Tenejakin/LM1/output/pdf/lm1-apriltag-36h11-id0-100mm-v1.0.0.pdf

# LM1 Camera Calibration Tag

AprilTag 36h11 - ID 0 - black outside edge is exactly 100 mm

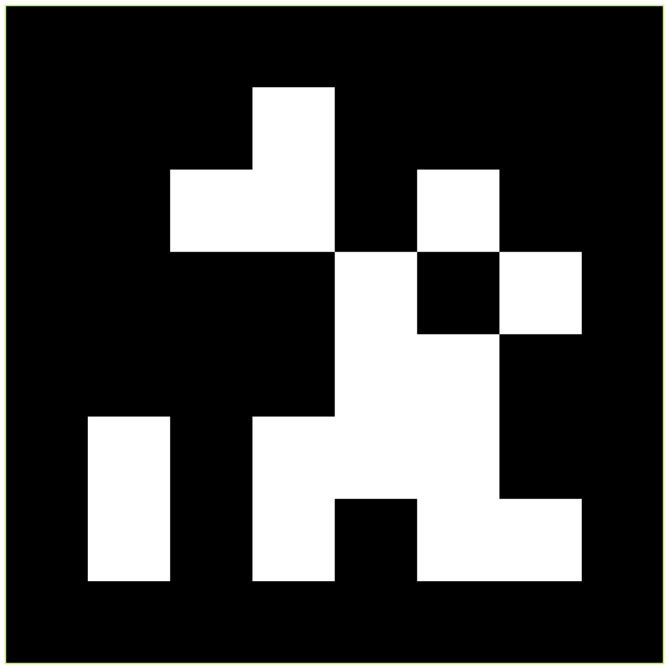
[picture p2: figure]

Use it to calibrate, then remove it before the hit.

1. Print at 100% / Actual size. Do not use Fit to page.
2. Measure the green outline: it must be 100 mm on every side.
3. Lay it flat beside the ball, capture calibration, then remove it without moving camera or mat.
4. Recalibrate whenever the camera, hitting mat, or ball location moves.
0 | 10 | 20 | 30 | 40 | 50 | 60 | 70 | 80 | 90 | 100

100 mm print check

LM1 AprilTag target v1.0.0 - keep flat, clean, and evenly lit
