Tenejakin/LM1/hardware/enclosure/stl/v0.6.0-stereo/preview.png

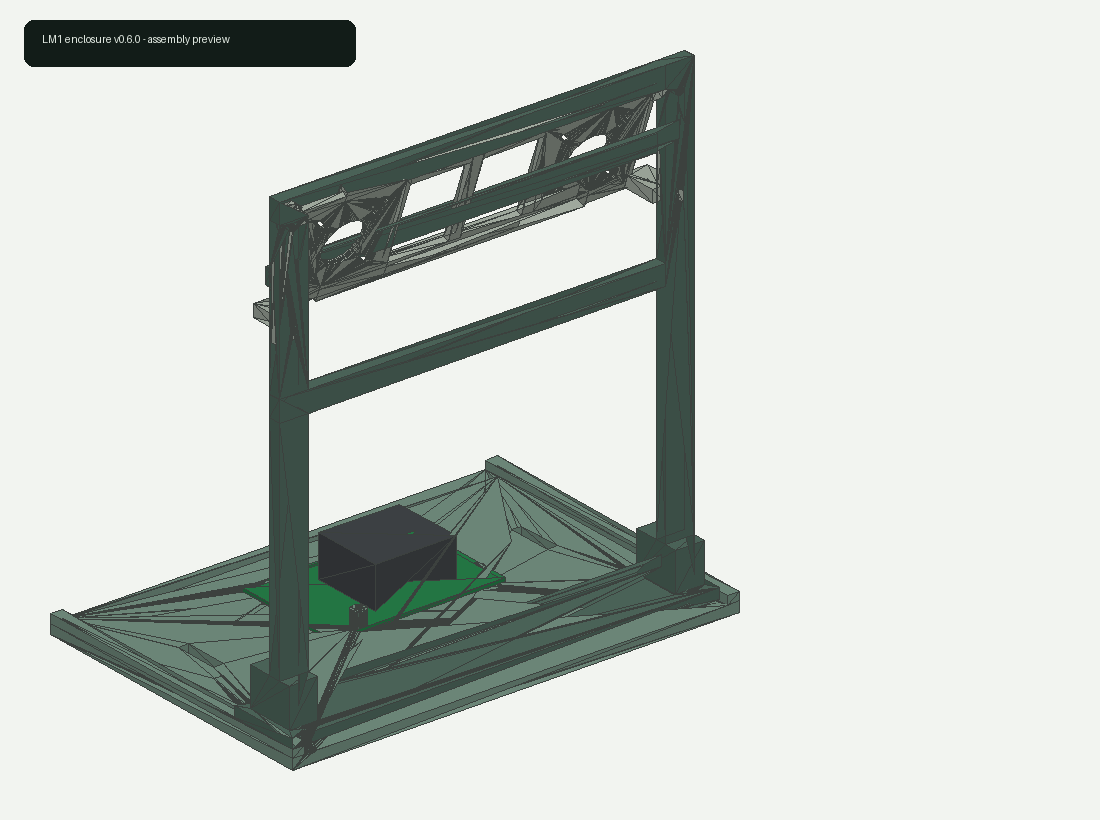
hardware/enclosure/stl/v0.6.0-stereo/preview.png
