Tenejakin/LM1/hardware/enclosure/stl/v0.7.2-vertical-development/preview.png

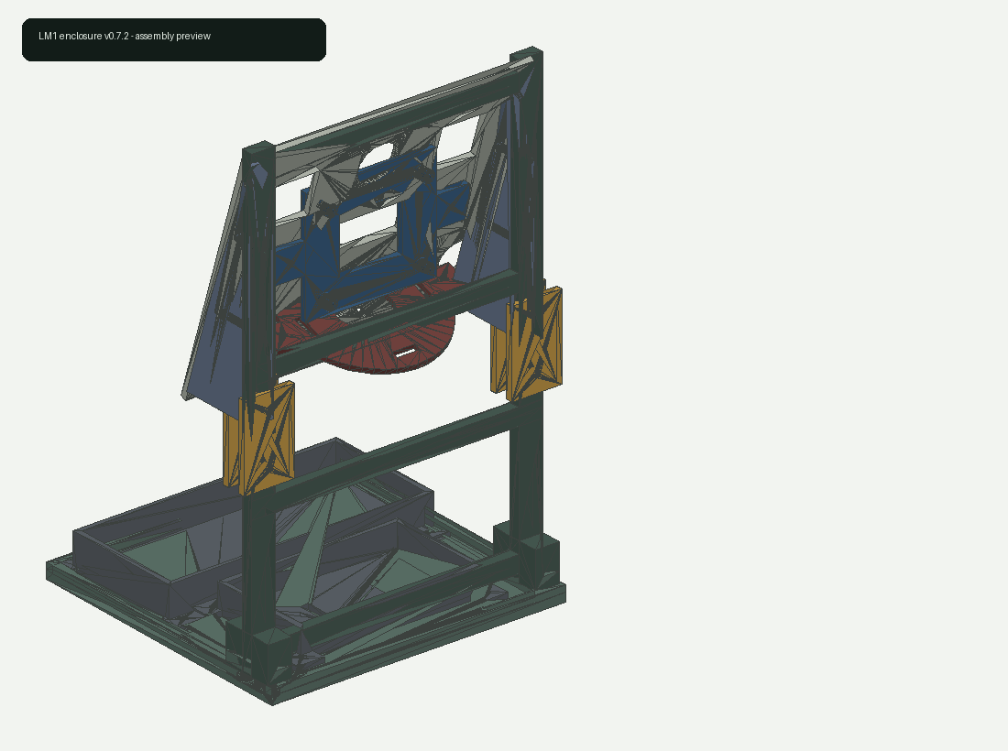
hardware/enclosure/stl/v0.7.2-vertical-development/preview.png
