Tenejakin/LM1/hardware/ir-crossbar-v1.0.1/preview.png

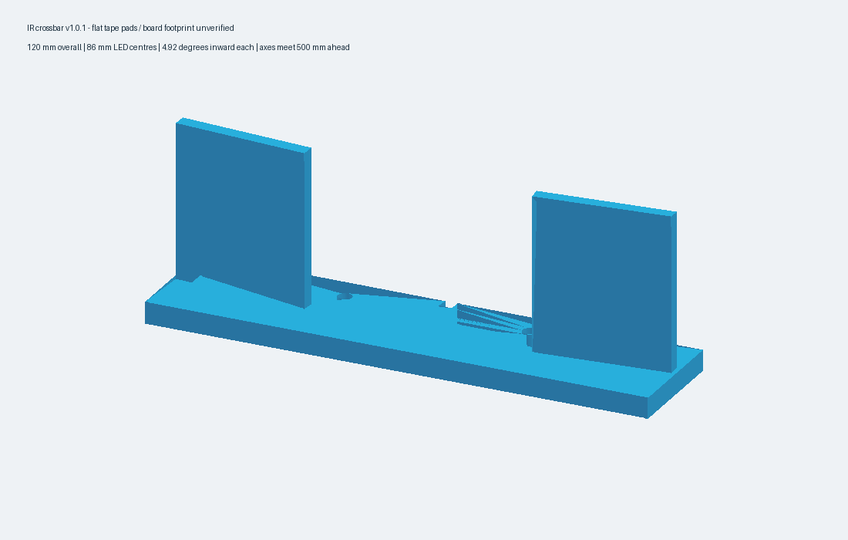
hardware/ir-crossbar-v1.0.1/preview.png
