Tenejakin/LM1/output/ir-denoise-v1.0.0/bilateral-display-4x.png

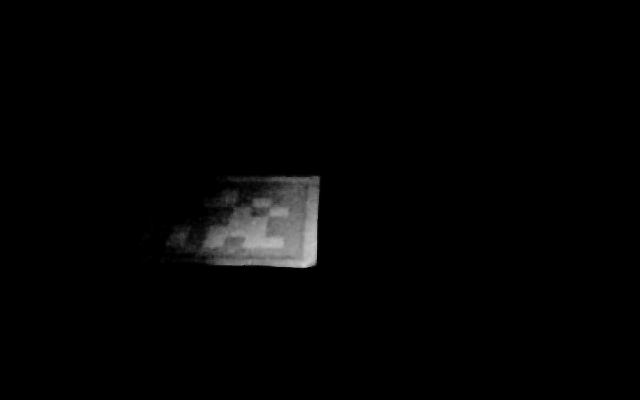
output/ir-denoise-v1.0.0/bilateral-display-4x.png
