Tenejakin/LM1/output/tag-recovery-v1.0.0/clahe.png

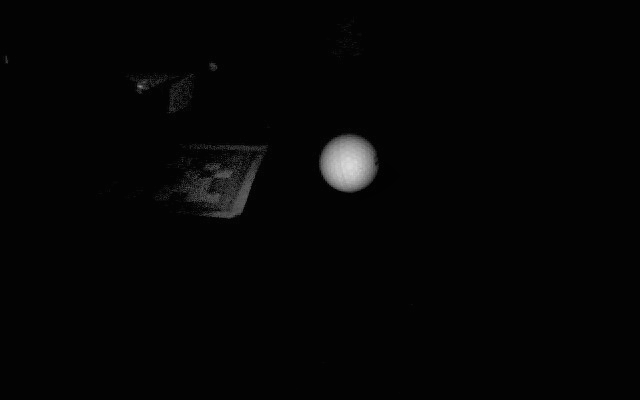
output/tag-recovery-v1.0.0/clahe.png
