Tenejakin/LM1/tmp/ai-review-latest/armed-ball-reference.png

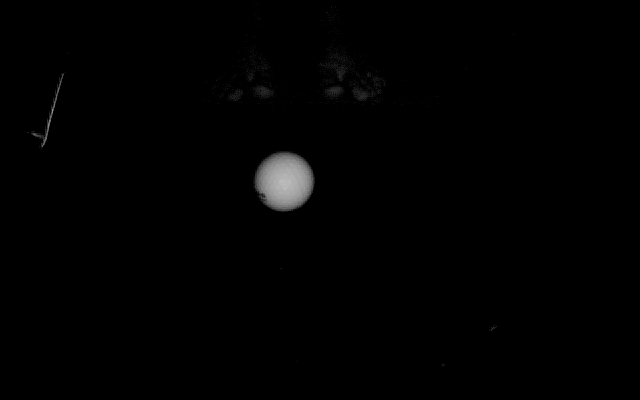
tmp/ai-review-latest/armed-ball-reference.png
