Tenejakin/LM1/tmp/ai-review-latest/frame-0175.jpg

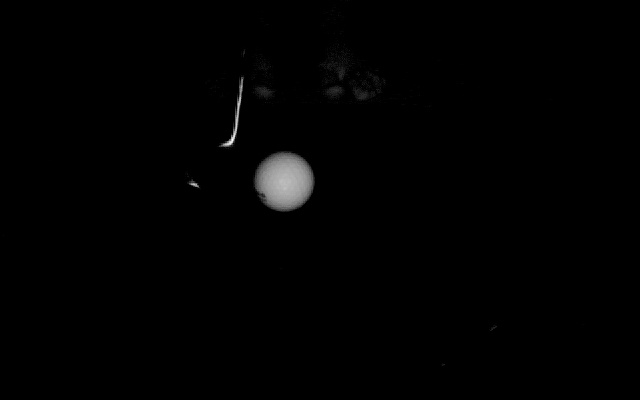
tmp/ai-review-latest/frame-0175.jpg
