Tenejakin/LM1/tmp/ai-review-latest/frame-0179.jpg

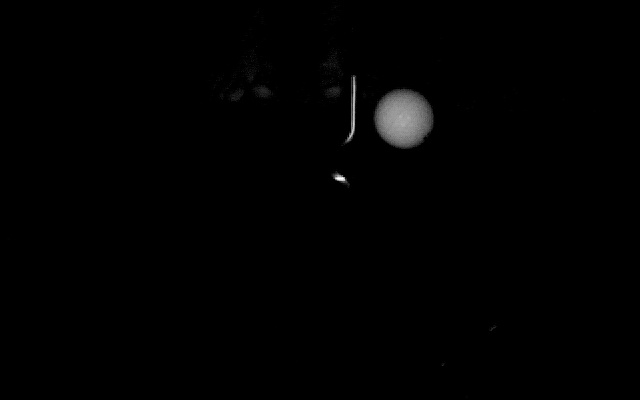
tmp/ai-review-latest/frame-0179.jpg
