Tenejakin/LM1/tmp/ai-review-latest/frame-0180.jpg

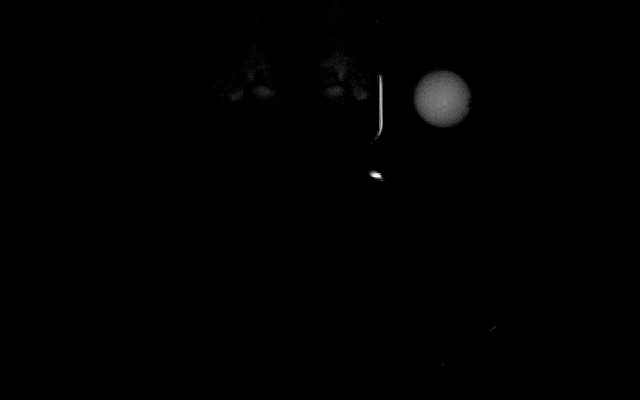
tmp/ai-review-latest/frame-0180.jpg
