Tenejakin/LM1/tmp/ai-review-latest/frame-0182.jpg

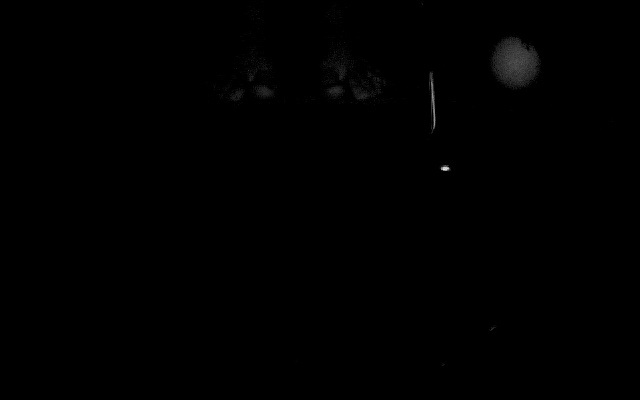
tmp/ai-review-latest/frame-0182.jpg
