Tenejakin/LM1/tmp/ai-review-marked-ball/frame-0185.jpg

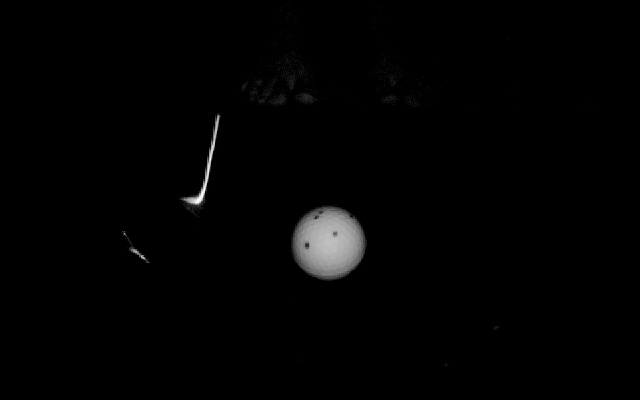
tmp/ai-review-marked-ball/frame-0185.jpg
