Tenejakin/LM1/tmp/ai-review-marked-ball/frame-0189.jpg

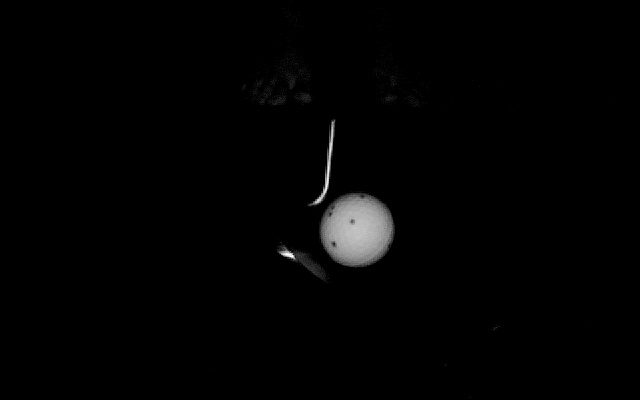
tmp/ai-review-marked-ball/frame-0189.jpg
