Tenejakin/LM1/tmp/ai-review-marked-ball/frame-0190.jpg

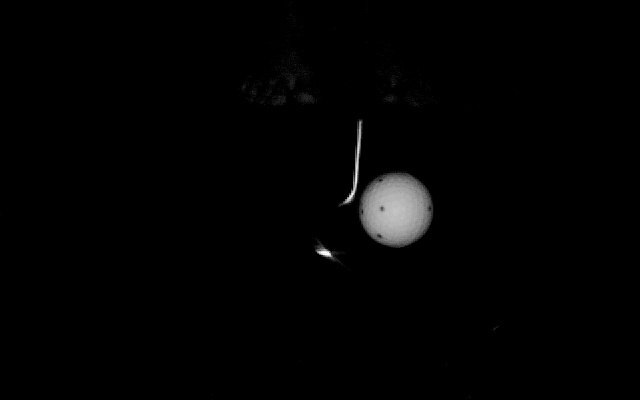
tmp/ai-review-marked-ball/frame-0190.jpg
