Tenejakin/LM1/tmp/ai-review-marked-ball/frame-0191.jpg

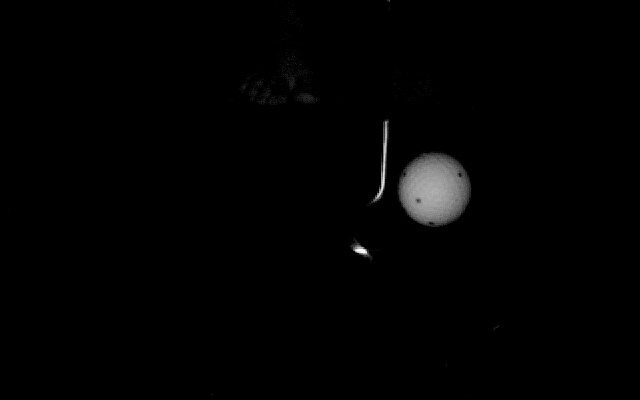
tmp/ai-review-marked-ball/frame-0191.jpg
