Tenejakin/LM1/tmp/ai-review-marked-ball/frame-0194.jpg

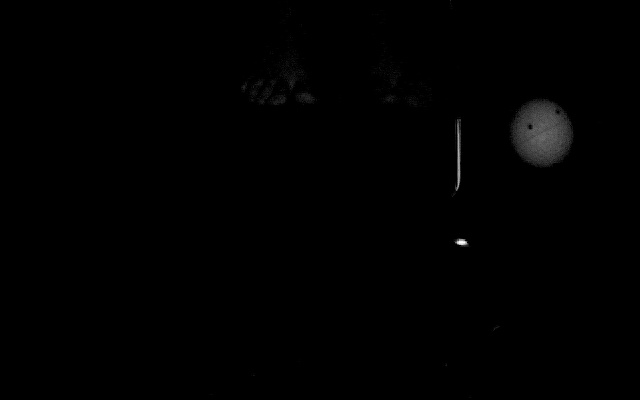
tmp/ai-review-marked-ball/frame-0194.jpg
