Tenejakin/LM1/tmp/ai-review-marked-ball/frame-0198.jpg

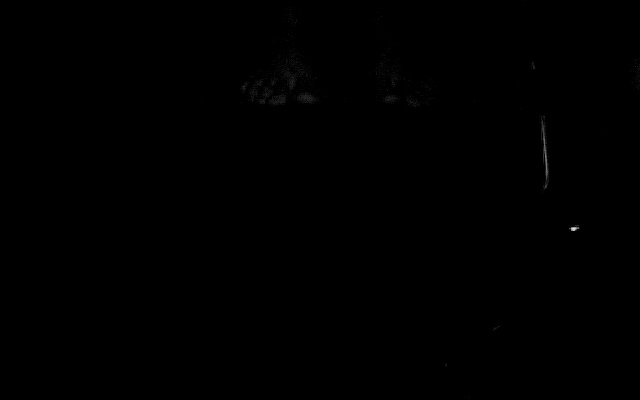
tmp/ai-review-marked-ball/frame-0198.jpg
