Tenejakin/LM1/tmp/apriltag/live-ball-after-reset.jpg

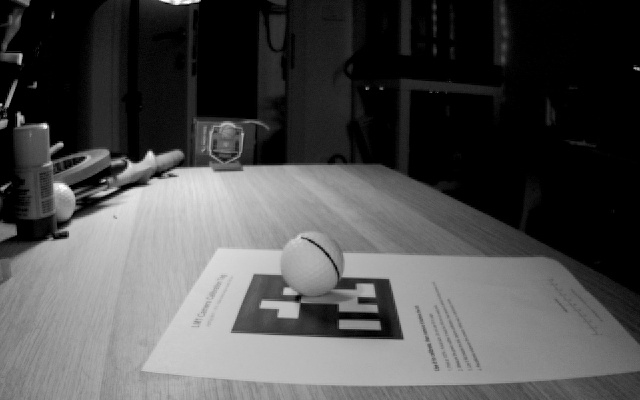
tmp/apriltag/live-ball-after-reset.jpg
