Tenejakin/LM1/tmp/apriltag/live-ball-diagnostic.jpg

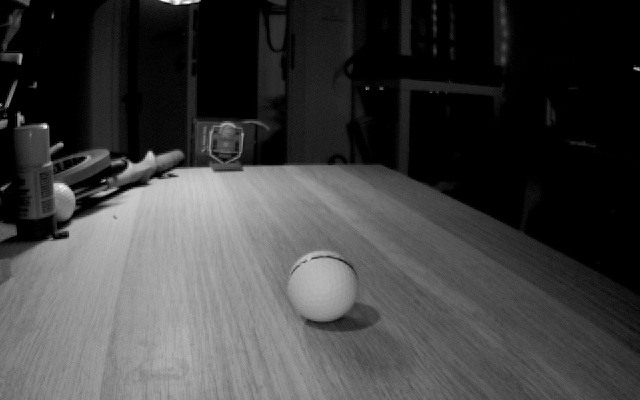
tmp/apriltag/live-ball-diagnostic.jpg
