Tenejakin/LM1/tmp/apriltag/live-ball-moved.jpg

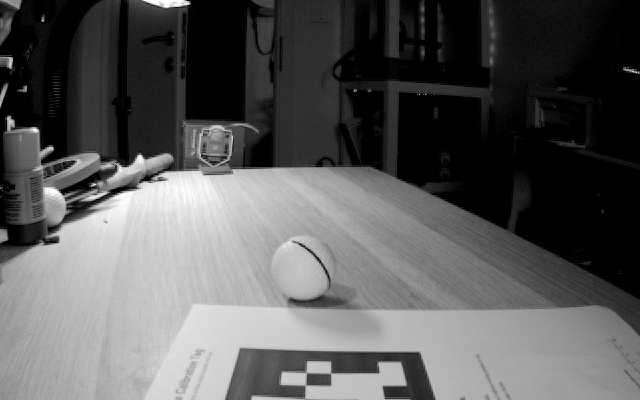
tmp/apriltag/live-ball-moved.jpg
