Tenejakin/LM1/tmp/apriltag/pre-0132-restart.jpg

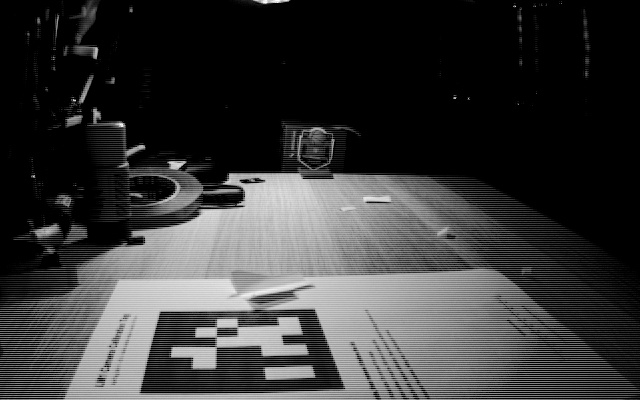
tmp/apriltag/pre-0132-restart.jpg
