Tenejakin/LM1/tmp/apriltag/render/page-1.png

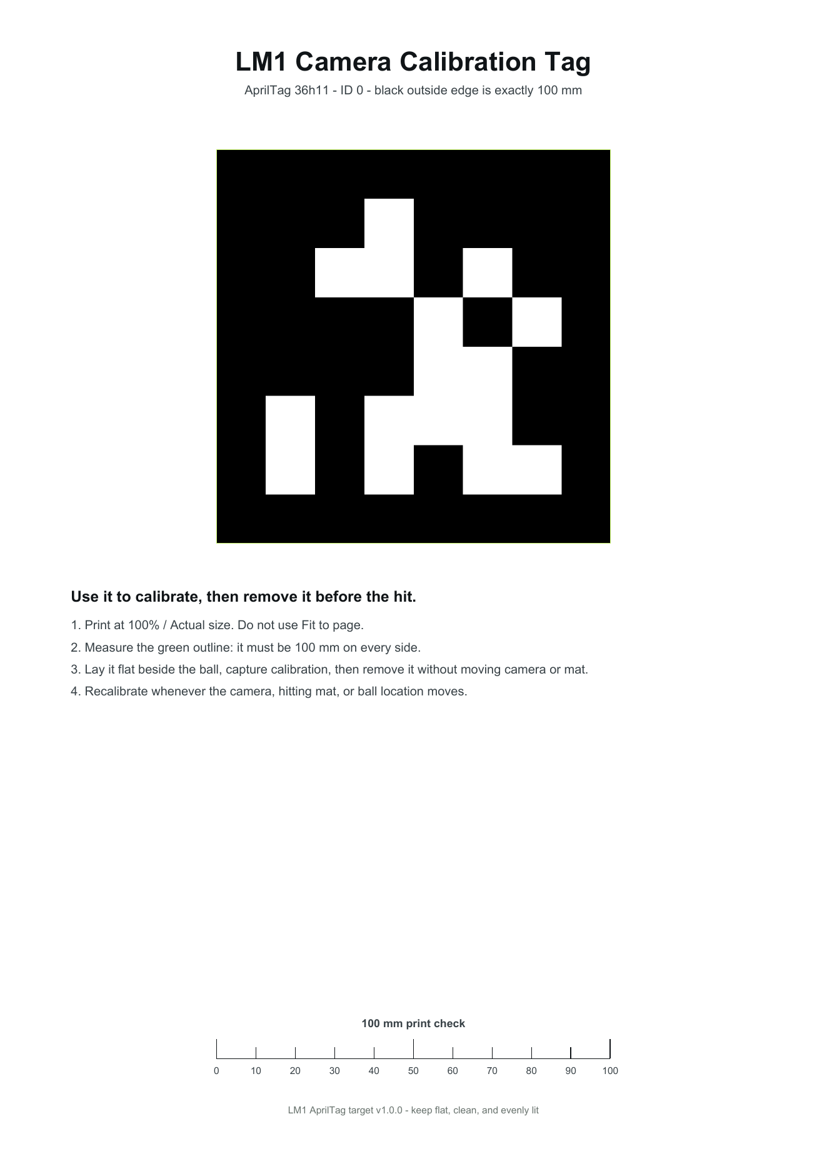
tmp/apriltag/render/page-1.png
