Tenejakin/LM1/tmp/camera-latest-focus-check-gain-current.jpg

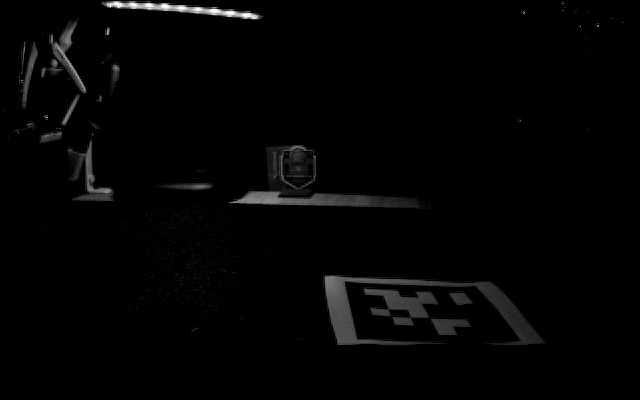
tmp/camera-latest-focus-check-gain-current.jpg
