Tenejakin/LM1/tmp/camera-latest-focus-check.jpg

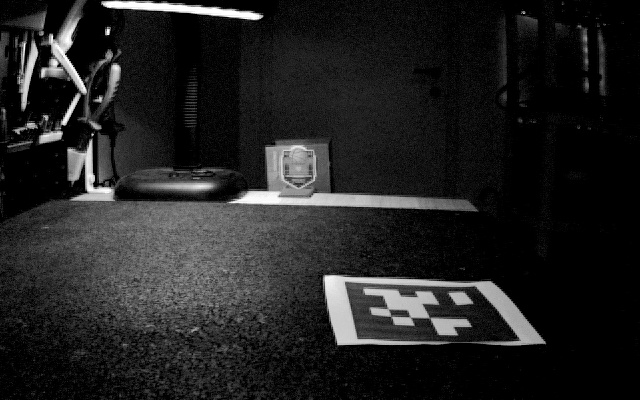
tmp/camera-latest-focus-check.jpg
