Tenejakin/LM1/tmp/camera-snapshot-2026-09-15-1404-v1.0.0.jpg

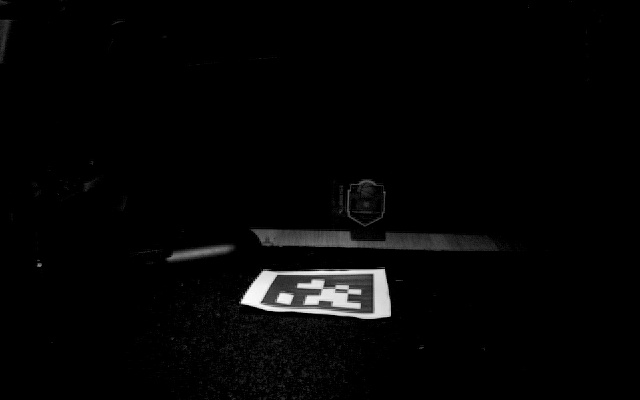
tmp/camera-snapshot-2026-09-15-1404-v1.0.0.jpg
