Tenejakin/LM1/tmp/ir-latest-review/contact-sheet.jpg

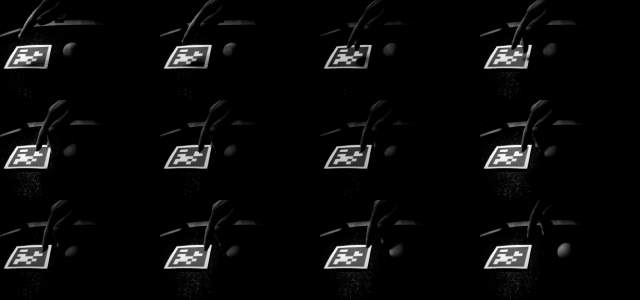
tmp/ir-latest-review/contact-sheet.jpg
