Tenejakin/LM1/tmp/ir-latest-review/ir-current-v1.0.0.jpg

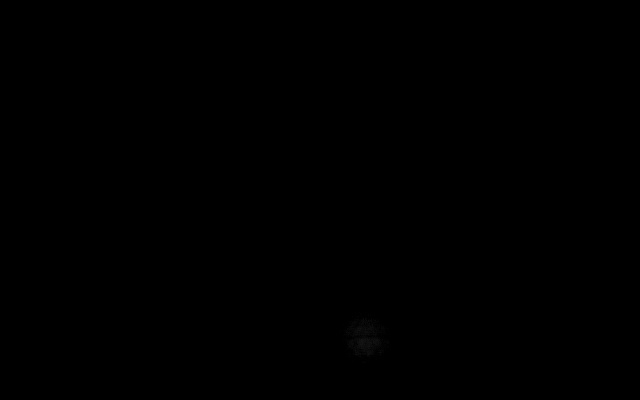
tmp/ir-latest-review/ir-current-v1.0.0.jpg
