Tenejakin/LM1/tmp/ir-latest-review/ir-current-v1.0.1.jpg

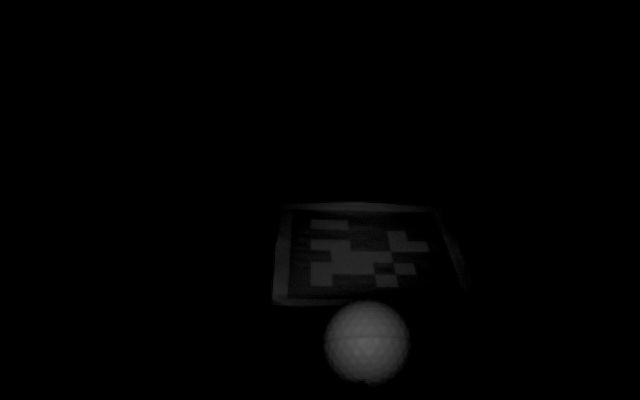
tmp/ir-latest-review/ir-current-v1.0.1.jpg
