Tenejakin/LM1/tmp/last-capture-1789337222749633794/frame-0422.jpg

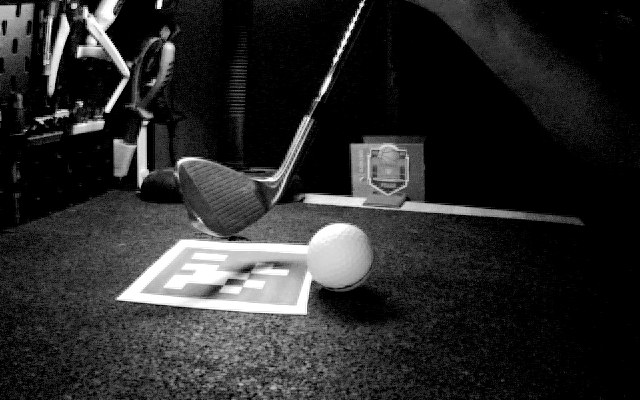
tmp/last-capture-1789337222749633794/frame-0422.jpg
