Tenejakin/LM1/tmp/last-shot-1789389599416398352/contact-sheet.jpg

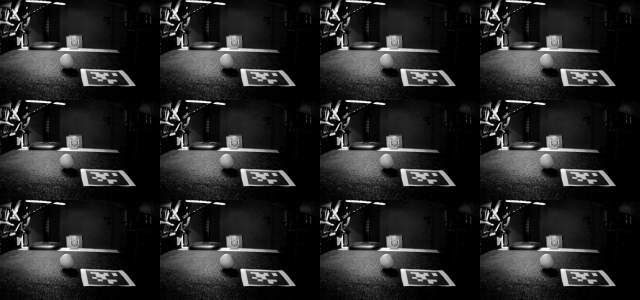
tmp/last-shot-1789389599416398352/contact-sheet.jpg
