Tenejakin/LM1/tmp/last-shot/contact-sheet.jpg

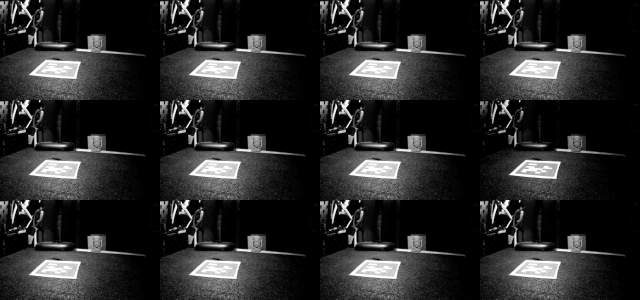
tmp/last-shot/contact-sheet.jpg
