Tenejakin/LM1/tmp/last-shot/frame-0410.jpg

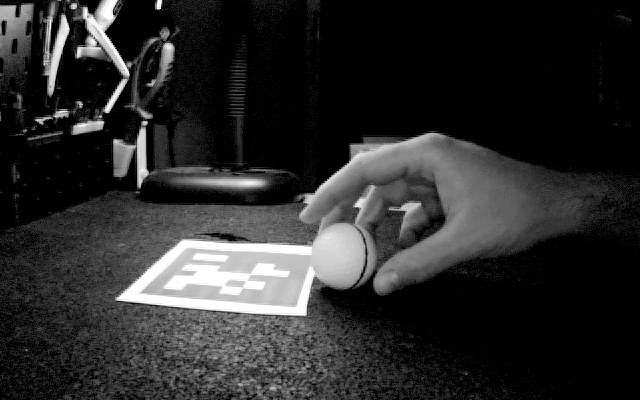
tmp/last-shot/frame-0410.jpg
