Tenejakin/LM1/tmp/last-shot/frame-0435.jpg

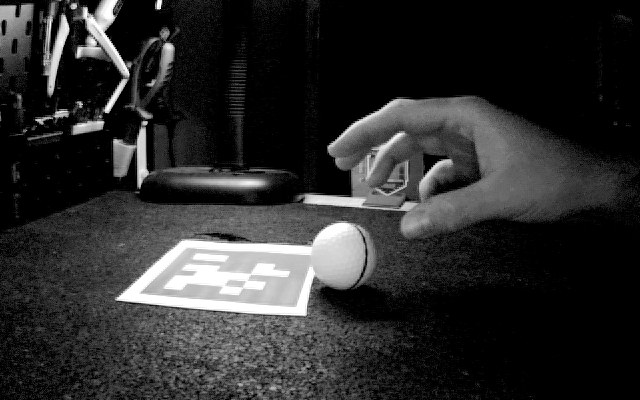
tmp/last-shot/frame-0435.jpg
