Tenejakin/LM1/tmp/last-shot/frame-0450.jpg

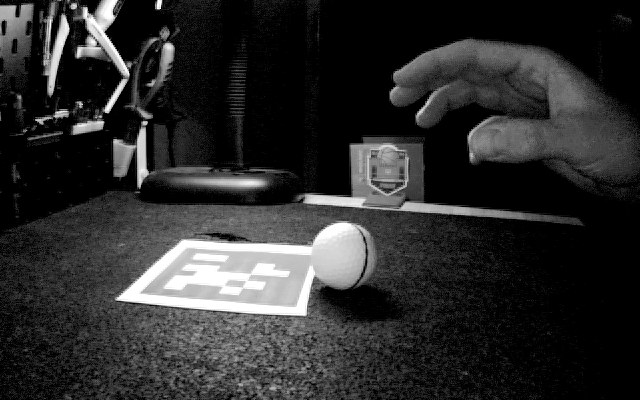
tmp/last-shot/frame-0450.jpg
