Tenejakin/LM1/tmp/last-shot/frame-0454.jpg

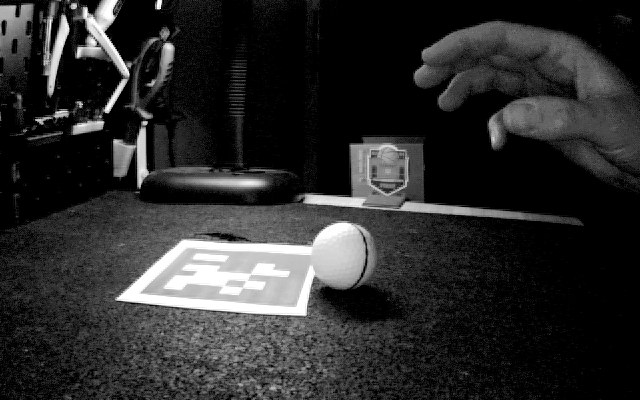
tmp/last-shot/frame-0454.jpg
