Tenejakin/LM1/tmp/last-shot/frame-0500.jpg

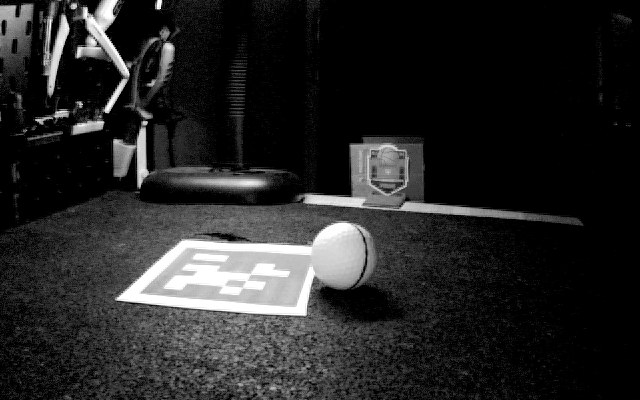
tmp/last-shot/frame-0500.jpg
