Tenejakin/LM1/tmp/rolling-review/capture-1788818826306235541/frame-0128.jpg

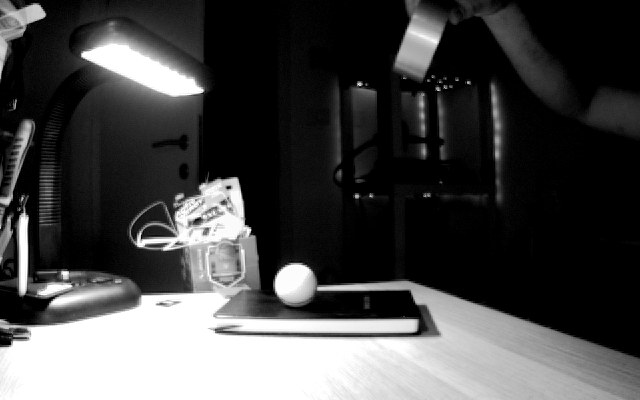
tmp/rolling-review/capture-1788818826306235541/frame-0128.jpg
