Tenejakin/LM1/tmp/shot2/frame-0300.jpg

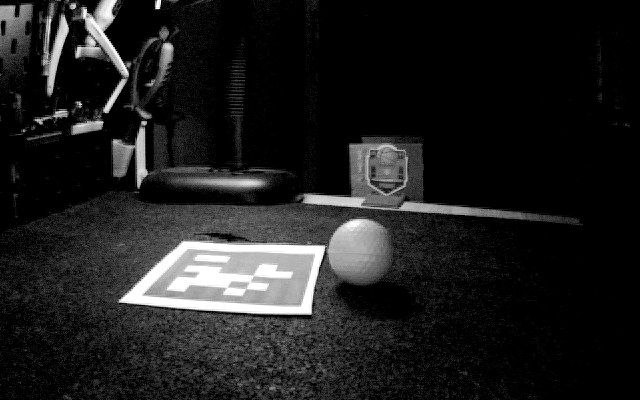
tmp/shot2/frame-0300.jpg
