Tenejakin/LM1/tmp/shot2/frame-0420.jpg

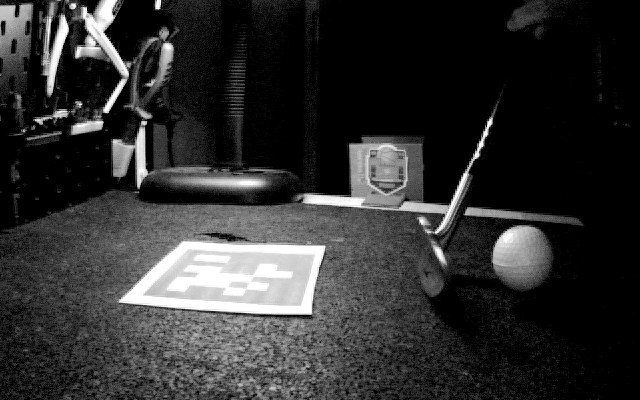
tmp/shot2/frame-0420.jpg
