Tenejakin/LM1/tmp/shot2/frame-0423.jpg

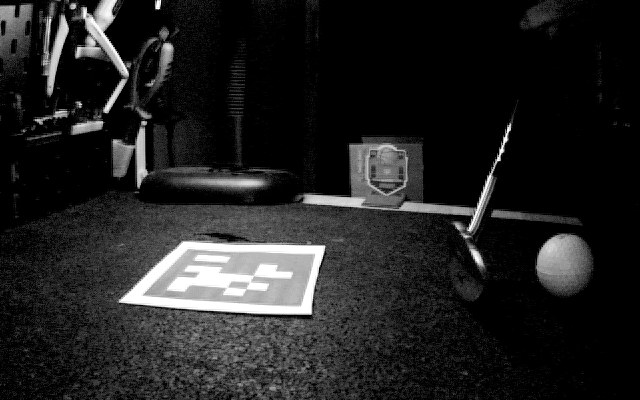
tmp/shot2/frame-0423.jpg
