Tenejakin/LM1/tmp/shot2/frame-0430.jpg

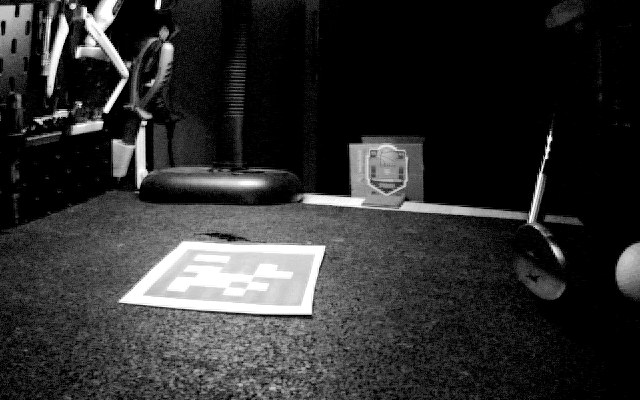
tmp/shot2/frame-0430.jpg
