Tenejakin/LM1/tmp/shot3/frame-0141.jpg

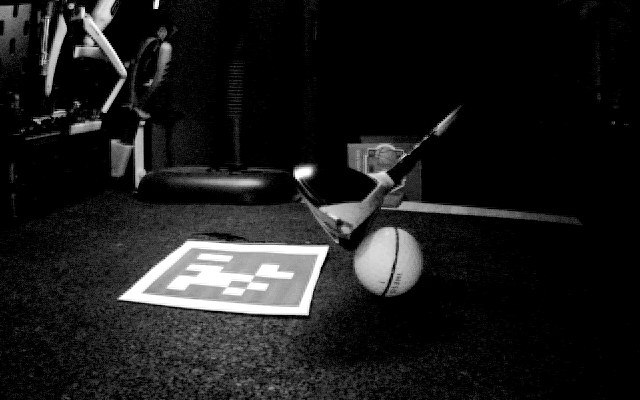
tmp/shot3/frame-0141.jpg
