Tenejakin/LM1/tmp/shot3/frame-0153.jpg

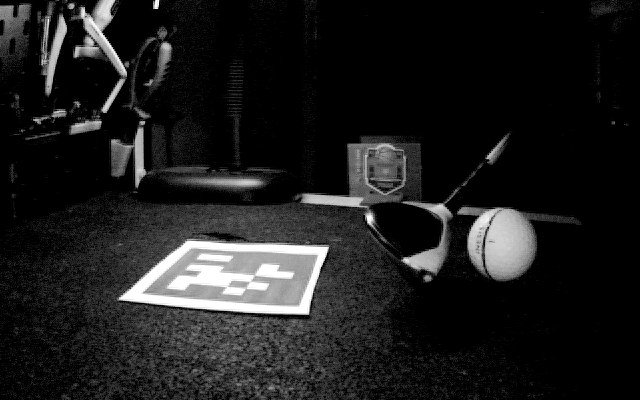
tmp/shot3/frame-0153.jpg
