Tenejakin/LM1/tmp/shot3/frame-0158.jpg

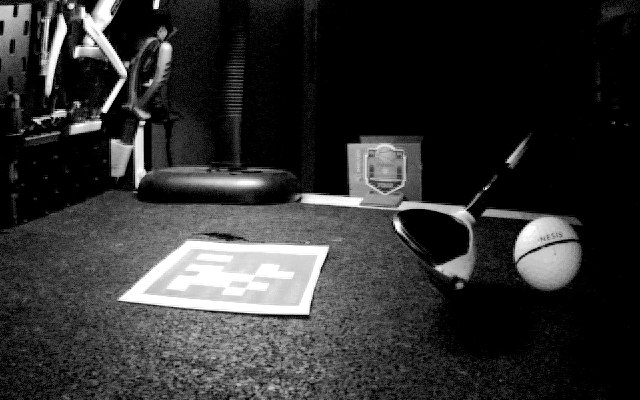
tmp/shot3/frame-0158.jpg
