Tenejakin/LM1/tmp/shot3/lm1-mask-140.png

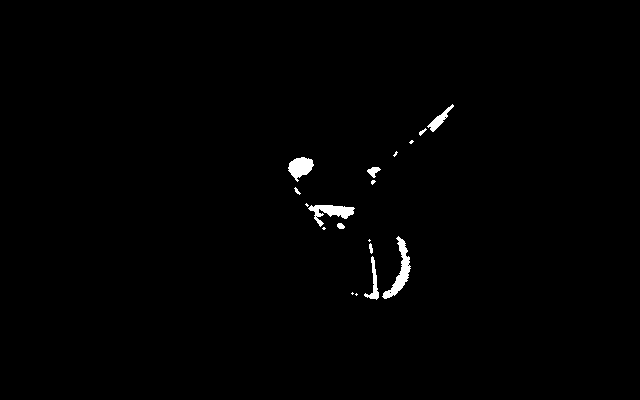
tmp/shot3/lm1-mask-140.png
