Tenejakin/LM1/tmp/shot3/lm1-mask-154.png

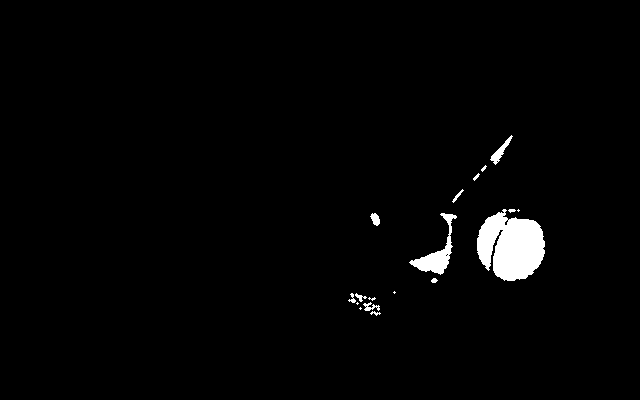
tmp/shot3/lm1-mask-154.png
