Tenejakin/LM1/tmp/shot4/frame-0175.jpg

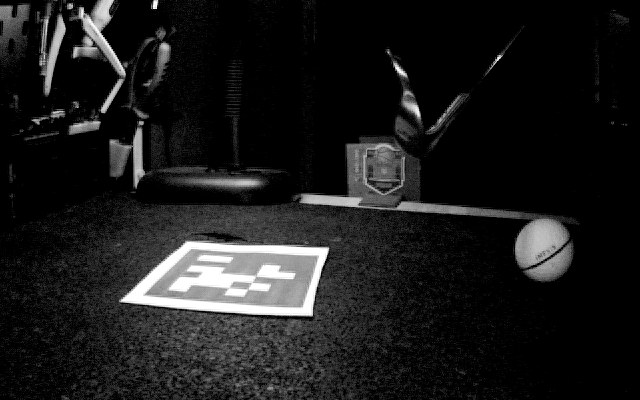
tmp/shot4/frame-0175.jpg
