Tenejakin/LM1/tmp/shot4/lm1-mask-170.png

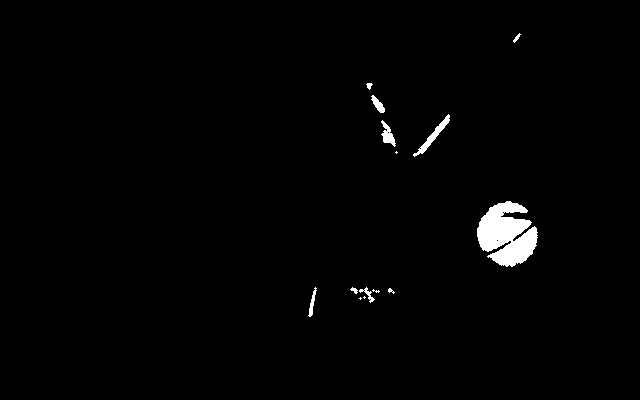
tmp/shot4/lm1-mask-170.png
