Tenejakin/LM1/tmp/shot-analysis-1789044823975054767/contact-sheet.jpg

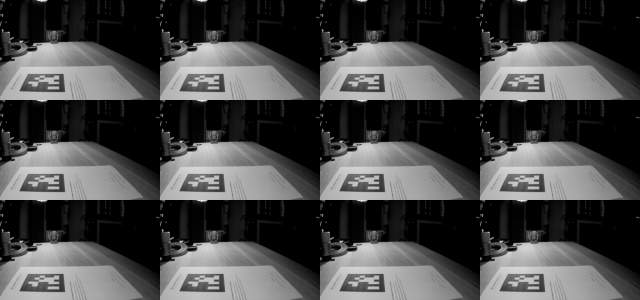
tmp/shot-analysis-1789044823975054767/contact-sheet.jpg
