Tenejakin/LM1/tmp/shot-analysis-1789044823975054767/frame-0000.jpg

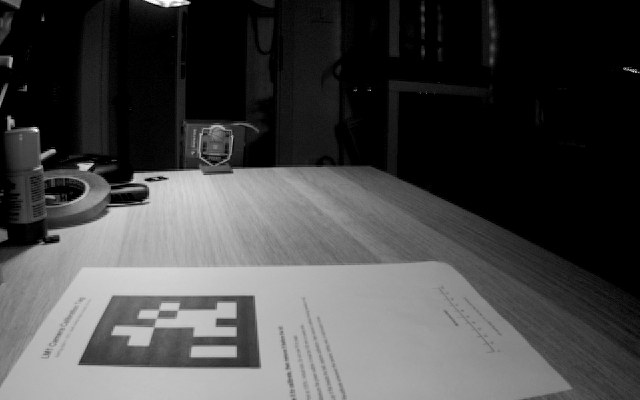
tmp/shot-analysis-1789044823975054767/frame-0000.jpg
