Tenejakin/LM1/hardware/enclosure/stl/v0.4.0/lm1_base_v0.4.0.stl

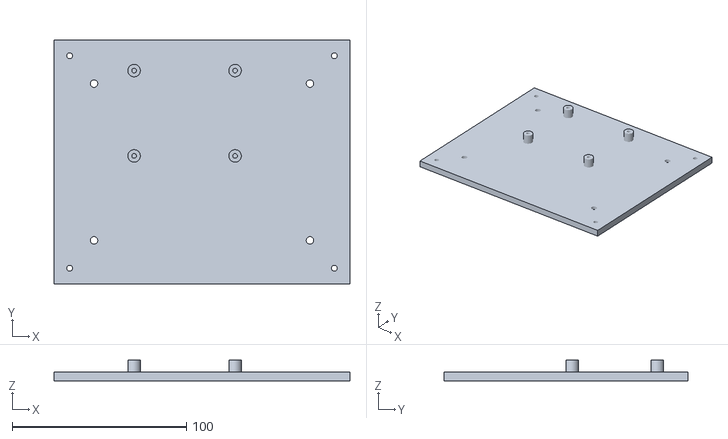
[picture p95: CAD file, 2026-09-18]
hardware/enclosure/stl/v0.4.0/lm1_base_v0.4.0.stl
170.0 x 140.0 x 12.0
