Tenejakin/LM1/hardware/enclosure/stl/v0.5.3-test/lm1_test_dual_camera_bracket_15deg_v0.5.3.stl

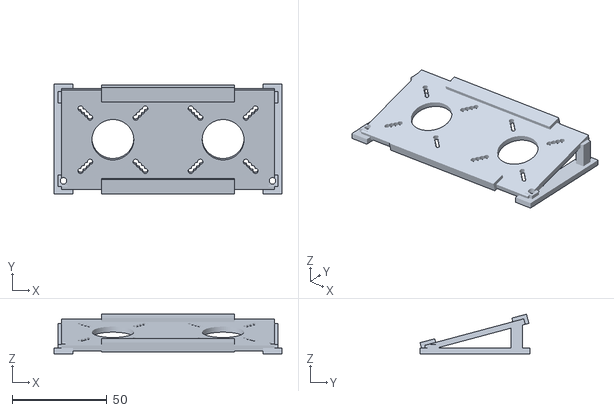
[picture p96: CAD file, 2026-10-06]
hardware/enclosure/stl/v0.5.3-test/lm1_test_dual_camera_bracket_15deg_v0.5.3.stl
120.0 x 58.0 x 20.9
