Tenejakin/LM1/hardware/enclosure/stl/v0.6.1-stereo-modular/lm1_dual_camera_bracket_20deg_v0.6.1.stl

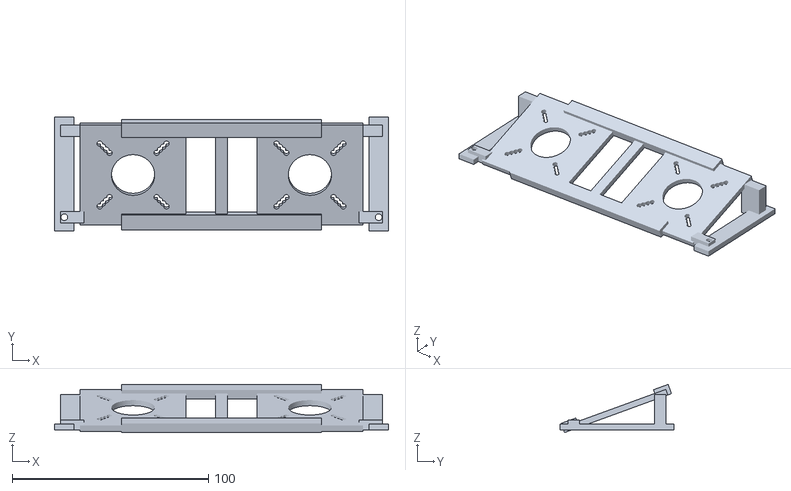
[picture p97: CAD file, 2026-10-06]
hardware/enclosure/stl/v0.6.1-stereo-modular/lm1_dual_camera_bracket_20deg_v0.6.1.stl
170.0 x 58.0 x 24.5
