Tenejakin/LM1/hardware/enclosure/stl/v0.7.2-vertical-development/lm1_pi5_head_cradle_v0.7.2.stl

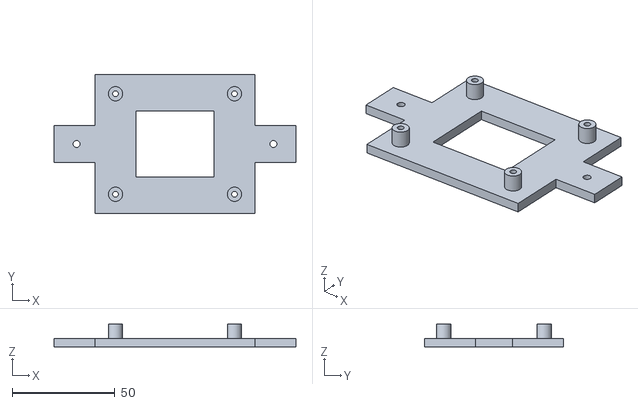
[picture p98: CAD file, 2026-10-06]
hardware/enclosure/stl/v0.7.2-vertical-development/lm1_pi5_head_cradle_v0.7.2.stl
118.0 x 68.0 x 11.0
