Tenejakin/LM1/hardware/enclosure/stl/v0.5.3-test/lm1_test_pi_tray_v0.5.3.stl

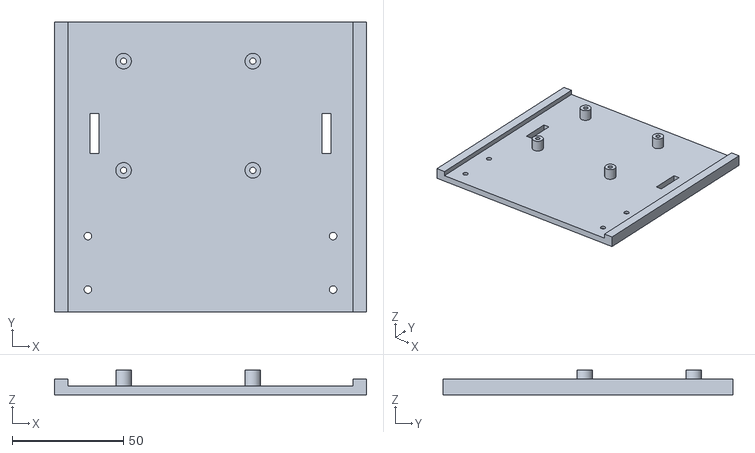
[picture p100: CAD file, 2026-09-18]
hardware/enclosure/stl/v0.5.3-test/lm1_test_pi_tray_v0.5.3.stl
140.0 x 130.0 x 11.0
