Tenejakin/LM1/hardware/enclosure/stl/v0.6.0-stereo/lm1_test_dual_camera_bracket_20deg_v0.6.0.stl

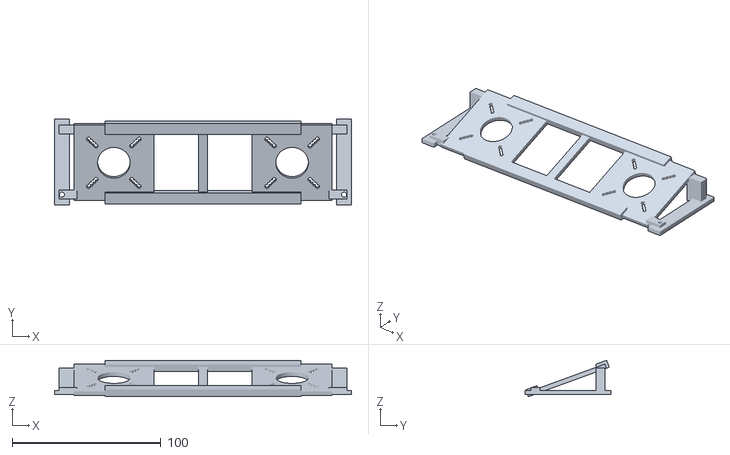
[picture p101: CAD file, 2026-10-06]
hardware/enclosure/stl/v0.6.0-stereo/lm1_test_dual_camera_bracket_20deg_v0.6.0.stl
200.0 x 58.0 x 24.5
