Tenejakin/LM1/hardware/enclosure/stl/v0.6.1-stereo-modular/lm1_mast_upper_v0.6.1.stl

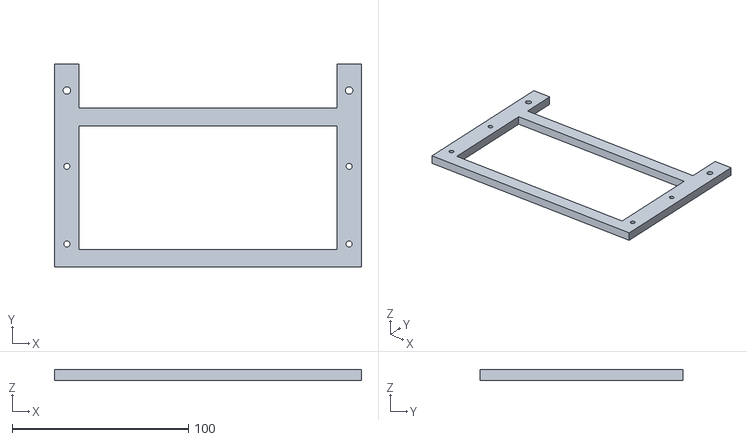
[picture p102: CAD file, 2026-10-06]
hardware/enclosure/stl/v0.6.1-stereo-modular/lm1_mast_upper_v0.6.1.stl
174.0 x 115.0 x 6.00
