Tenejakin/LM1/hardware/enclosure/stl/v0.7.2-vertical-development/lm1_pi5_cover_v0.7.2.stl

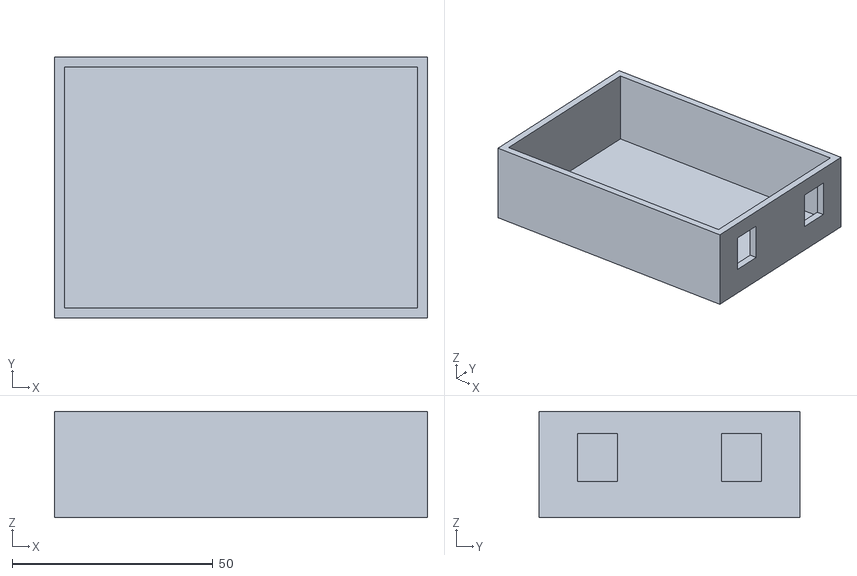
[picture p103: CAD file, 2026-10-06]
hardware/enclosure/stl/v0.7.2-vertical-development/lm1_pi5_cover_v0.7.2.stl
93.0 x 65.0 x 26.5
