Tenejakin/LM1/hardware/enclosure/stl/v0.4.0/lm1_window_retainer_v0.4.0.stl

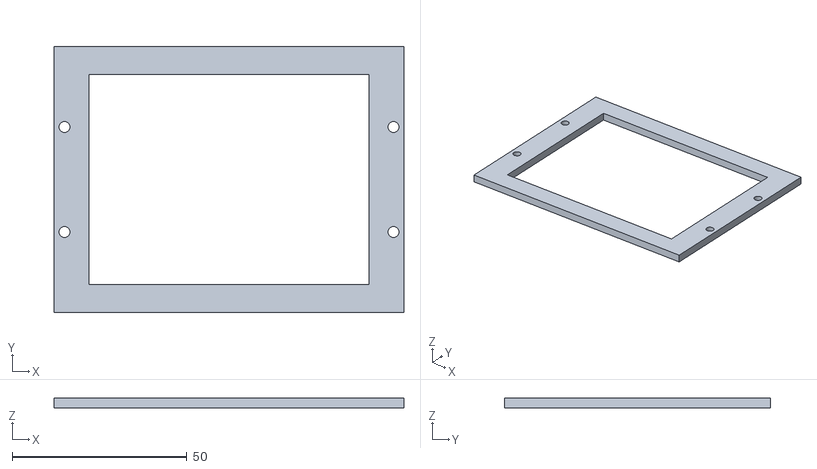
[picture p104: CAD file, 2026-09-18]
hardware/enclosure/stl/v0.4.0/lm1_window_retainer_v0.4.0.stl
100.0 x 76.0 x 3.00
