Tenejakin/LM1/hardware/enclosure/stl/v0.5.3-test/lm1_test_camera_mast_v0.5.3.stl

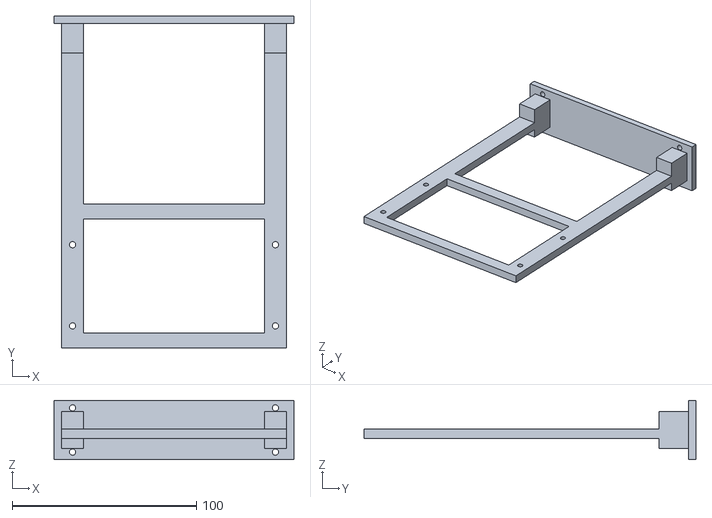
[picture p105: CAD file, 2026-09-18]
hardware/enclosure/stl/v0.5.3-test/lm1_test_camera_mast_v0.5.3.stl
130.0 x 180.0 x 32.0
