Tenejakin/LM1/hardware/enclosure/stl/v0.6.0-stereo/lm1_test_pi_tray_v0.6.0.stl

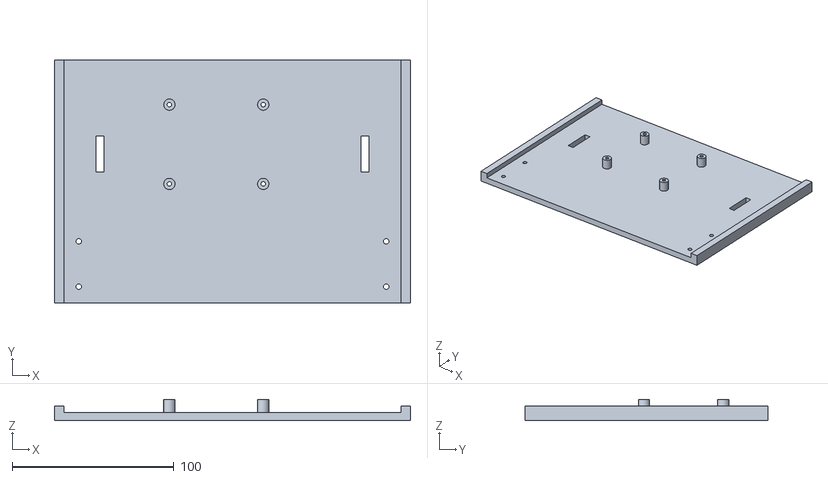
[picture p106: CAD file, 2026-10-06]
hardware/enclosure/stl/v0.6.0-stereo/lm1_test_pi_tray_v0.6.0.stl
220.0 x 150.0 x 13.0
