Tenejakin/LM1/hardware/enclosure/stl/v0.6.1-stereo-modular/lm1_mast_splice_plate_v0.6.1.stl

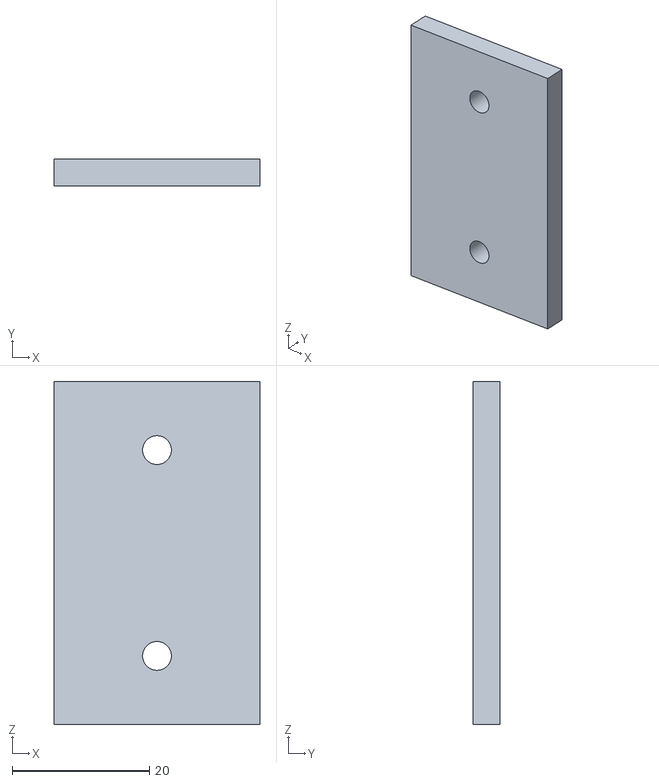
[picture p107: CAD file, 2026-10-06]
hardware/enclosure/stl/v0.6.1-stereo-modular/lm1_mast_splice_plate_v0.6.1.stl
30.0 x 4.00 x 50.0
