Tenejakin/LM1/hardware/enclosure/stl/v0.7.2-vertical-development/lm1_power_pack_lid_v0.7.2.stl

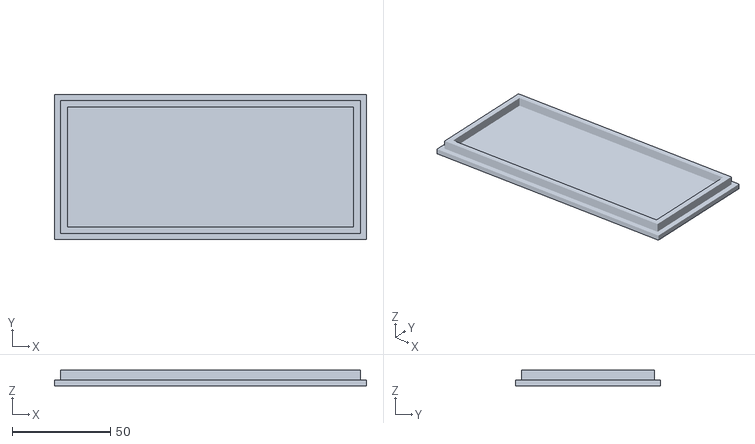
[picture p108: CAD file, 2026-10-06]
hardware/enclosure/stl/v0.7.2-vertical-development/lm1_power_pack_lid_v0.7.2.stl
159.0 x 74.0 x 8.00
