Tenejakin/LM1/hardware/enclosure/stl/v0.4.0/lm1_camera_mount_13deg_v0.4.0.stl

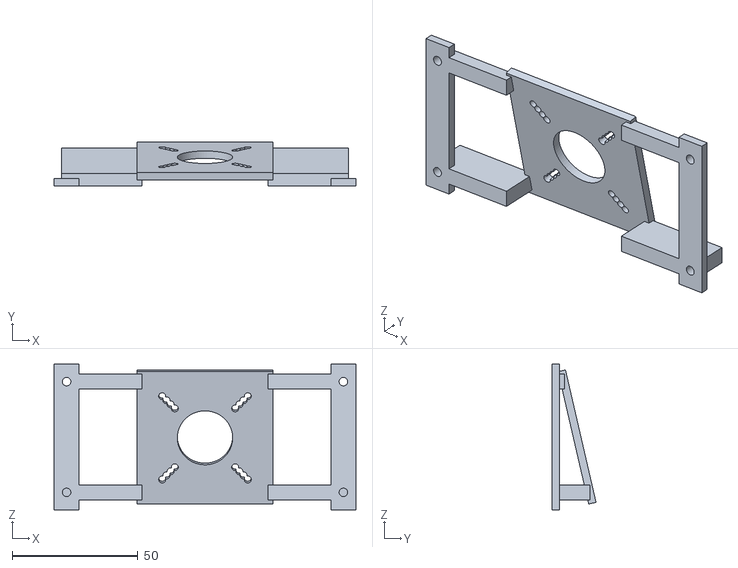
[picture p109: CAD file, 2026-09-18]
hardware/enclosure/stl/v0.4.0/lm1_camera_mount_13deg_v0.4.0.stl
120.0 x 17.5 x 58.0
