Tenejakin/LM1/hardware/enclosure/stl/v0.7.2-vertical-development/lm1_vertical_camera_light_carrier_v0.7.2.stl

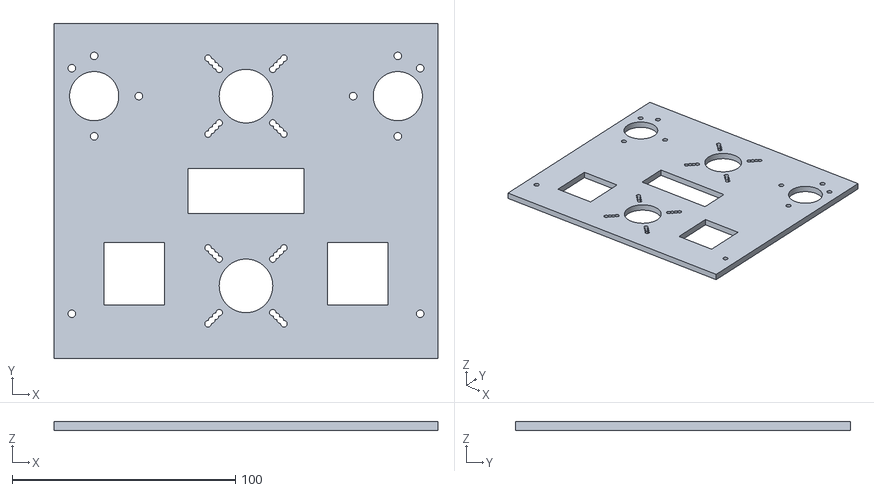
[picture p110: CAD file, 2026-10-06]
hardware/enclosure/stl/v0.7.2-vertical-development/lm1_vertical_camera_light_carrier_v0.7.2.stl
172.0 x 150.0 x 4.00
