Tenejakin/LM1/hardware/enclosure/stl/v0.4.0/lm1_led_adapter_v0.4.0.stl

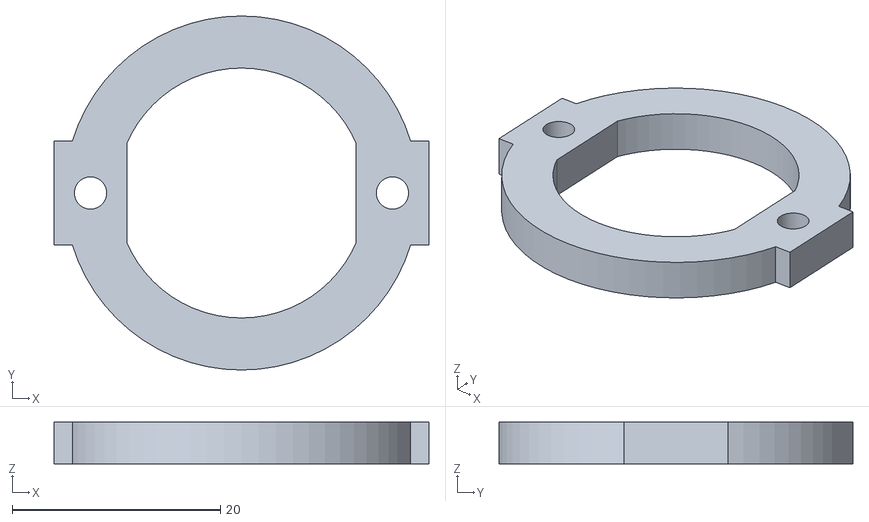
[picture p111: CAD file, 2026-09-18]
hardware/enclosure/stl/v0.4.0/lm1_led_adapter_v0.4.0.stl
36.0 x 34.0 x 4.00
