Tenejakin/LM1/hardware/enclosure/stl/v0.6.1-stereo-modular/lm1_stereo_tray_v0.6.1.stl

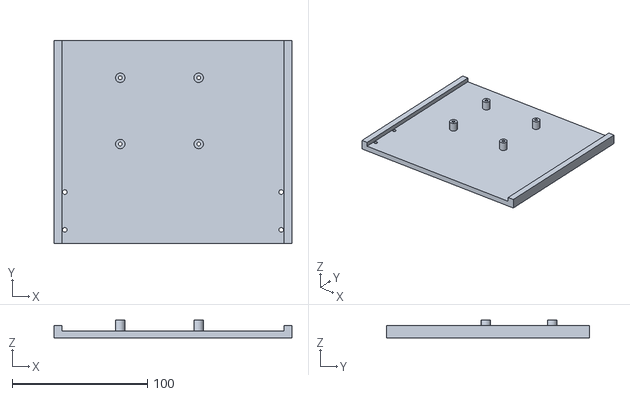
[picture p112: CAD file, 2026-10-06]
hardware/enclosure/stl/v0.6.1-stereo-modular/lm1_stereo_tray_v0.6.1.stl
176.0 x 150.0 x 13.0
