Tenejakin/LM1/hardware/enclosure/stl/v0.7.2-vertical-development/lm1_ir_ring_retainer_80mm_v0.7.2.stl

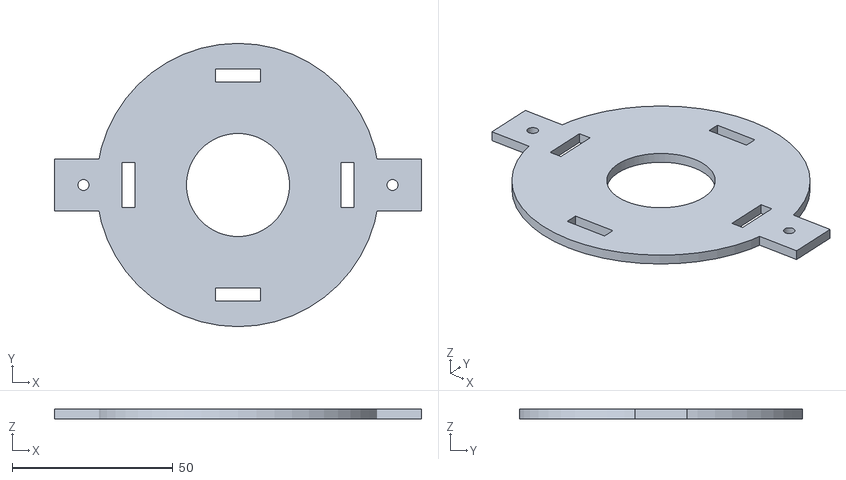
[picture p113: CAD file, 2026-10-06]
hardware/enclosure/stl/v0.7.2-vertical-development/lm1_ir_ring_retainer_80mm_v0.7.2.stl
114.0 x 88.0 x 3.00
