Tenejakin/LM1/hardware/enclosure/stl/v0.7.2-vertical-development/lm1_vertical_mast_lower_v0.7.2.stl

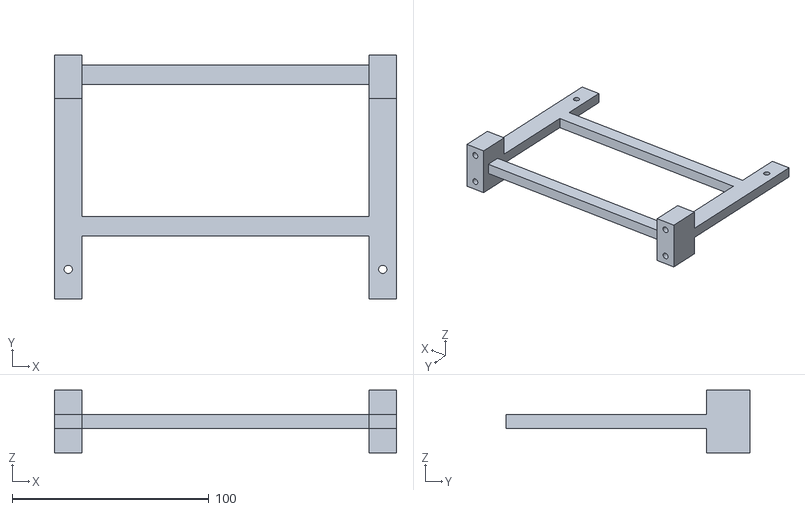
[picture p114: CAD file, 2026-10-06]
hardware/enclosure/stl/v0.7.2-vertical-development/lm1_vertical_mast_lower_v0.7.2.stl
174.0 x 124.0 x 32.0
