Tenejakin/LM1/hardware/enclosure/stl/v0.4.0/lm1_front_sensor_panel_v0.4.0.stl

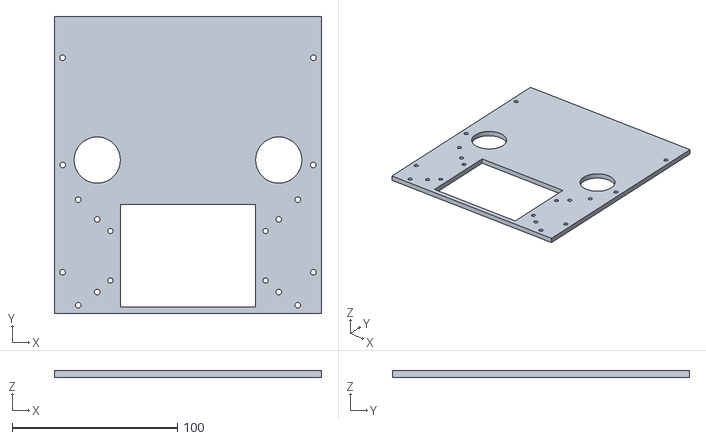
[picture p115: CAD file, 2026-09-18]
hardware/enclosure/stl/v0.4.0/lm1_front_sensor_panel_v0.4.0.stl
162.0 x 180.0 x 4.00
