Tenejakin/LM1/hardware/enclosure/stl/v0.7.2-vertical-development/lm1_side_light_pod_20mm_v0.7.2.stl

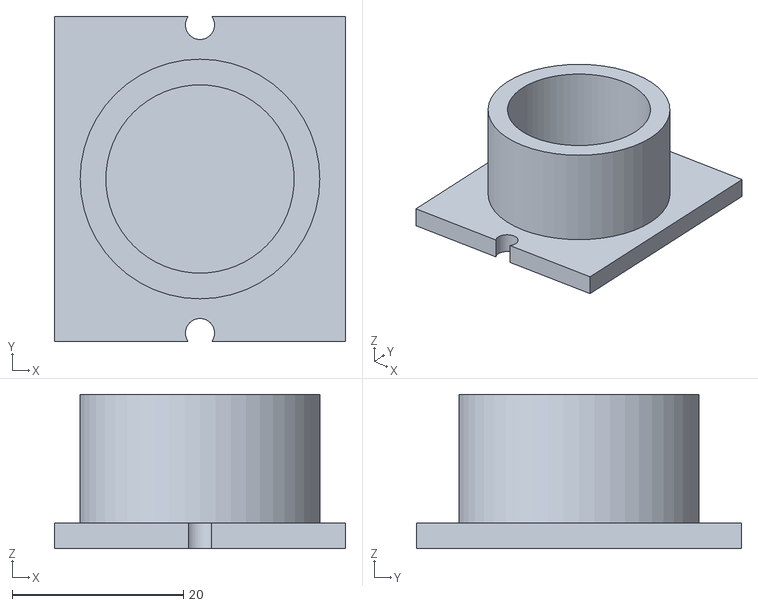
[picture p116: CAD file, 2026-10-06]
hardware/enclosure/stl/v0.7.2-vertical-development/lm1_side_light_pod_20mm_v0.7.2.stl
34.0 x 38.0 x 18.0
