Tenejakin/LM1/hardware/enclosure/stl/v0.4.0/lm1_top_swivel_v0.4.0.stl

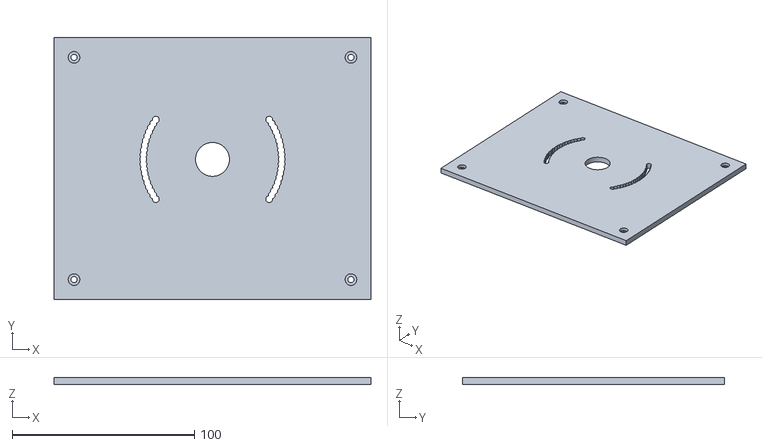
[picture p117: CAD file, 2026-09-18]
hardware/enclosure/stl/v0.4.0/lm1_top_swivel_v0.4.0.stl
174.0 x 144.0 x 4.00
