Tenejakin/LM1/hardware/enclosure/stl/v0.4.0/lm1_oled_tilt_cradle_35deg_v0.4.0.stl

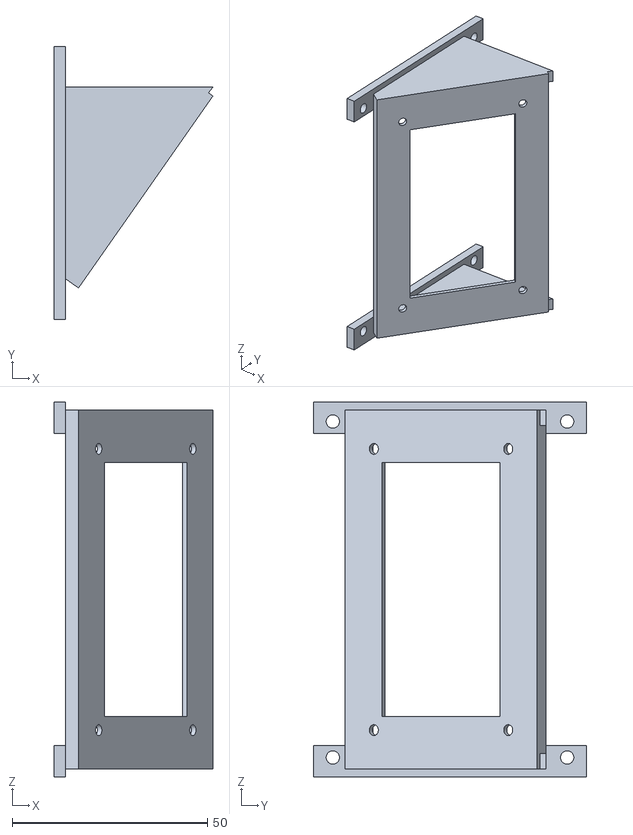
[picture p118: CAD file, 2026-09-18]
hardware/enclosure/stl/v0.4.0/lm1_oled_tilt_cradle_35deg_v0.4.0.stl
40.7 x 70.0 x 96.0
