Tenejakin/LM1/hardware/enclosure/stl/v0.7.2-vertical-development/lm1_vertical_base_v0.7.2.stl

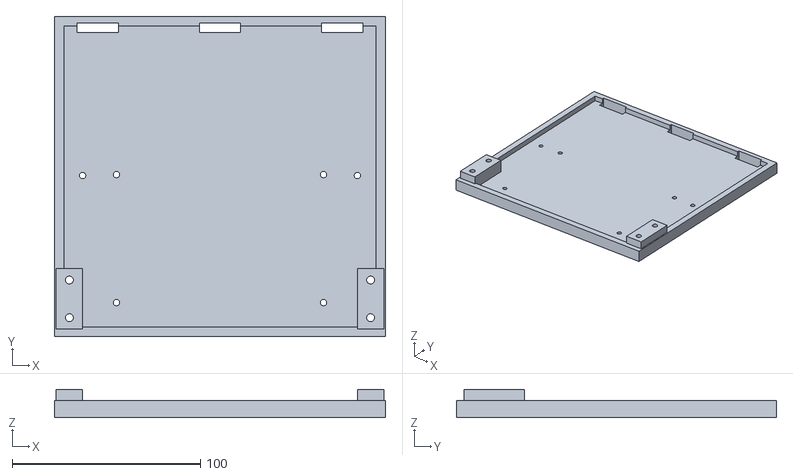
[picture p119: CAD file, 2026-10-06]
hardware/enclosure/stl/v0.7.2-vertical-development/lm1_vertical_base_v0.7.2.stl
176.0 x 170.0 x 15.0
