Tenejakin/LM1/hardware/enclosure/stl/v0.4.0/lm1_oled_retainer_v0.4.0.stl

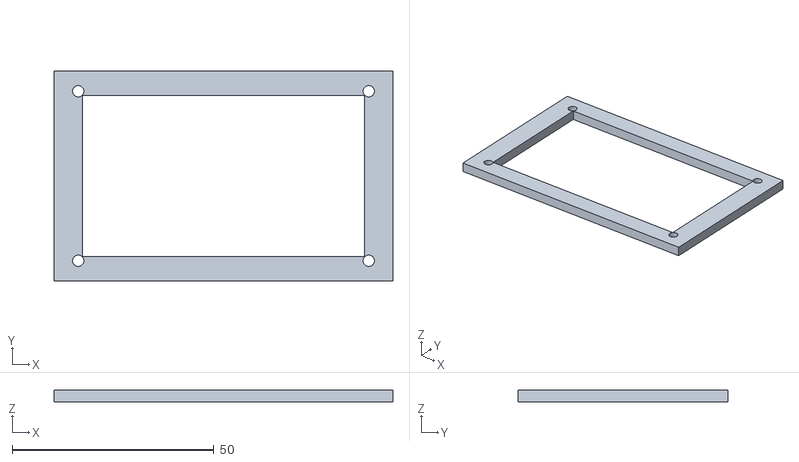
[picture p120: CAD file, 2026-09-18]
hardware/enclosure/stl/v0.4.0/lm1_oled_retainer_v0.4.0.stl
84.0 x 52.0 x 3.00
