Tenejakin/LM1/hardware/enclosure/stl/v0.7.2-vertical-development/lm1_ir_ring_shroud_80mm_v0.7.2.stl

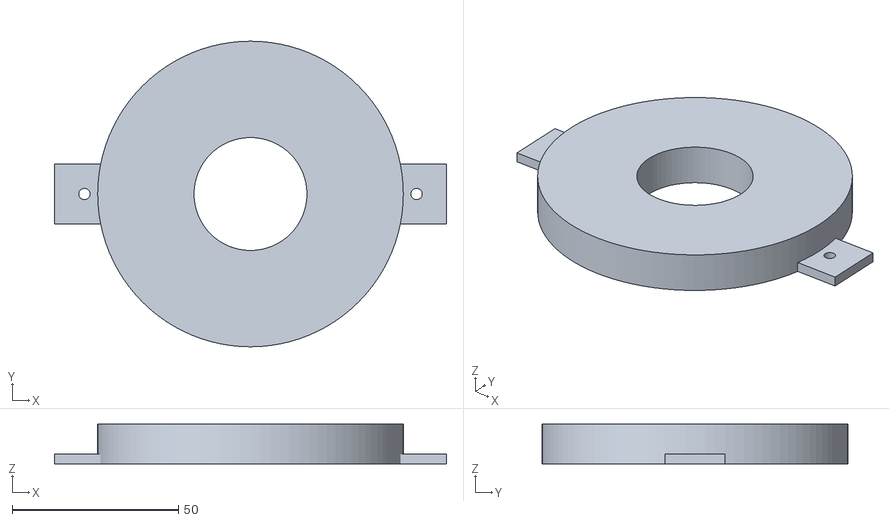
[picture p121: CAD file, 2026-10-06]
hardware/enclosure/stl/v0.7.2-vertical-development/lm1_ir_ring_shroud_80mm_v0.7.2.stl
118.0 x 92.0 x 12.0
