Tenejakin/LM1/hardware/enclosure/stl/v0.4.0/lm1_rear_service_panel_v0.4.0.stl

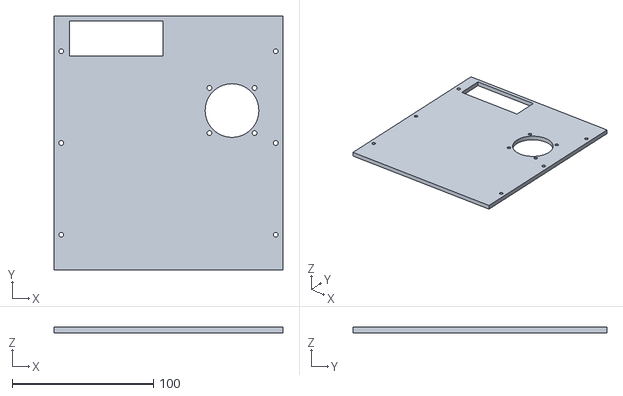
[picture p122: CAD file, 2026-09-18]
hardware/enclosure/stl/v0.4.0/lm1_rear_service_panel_v0.4.0.stl
162.0 x 180.0 x 4.00
