Tenejakin/LM1/hardware/enclosure/stl/v0.4.0/lm1_sun_hood_v0.4.0.stl

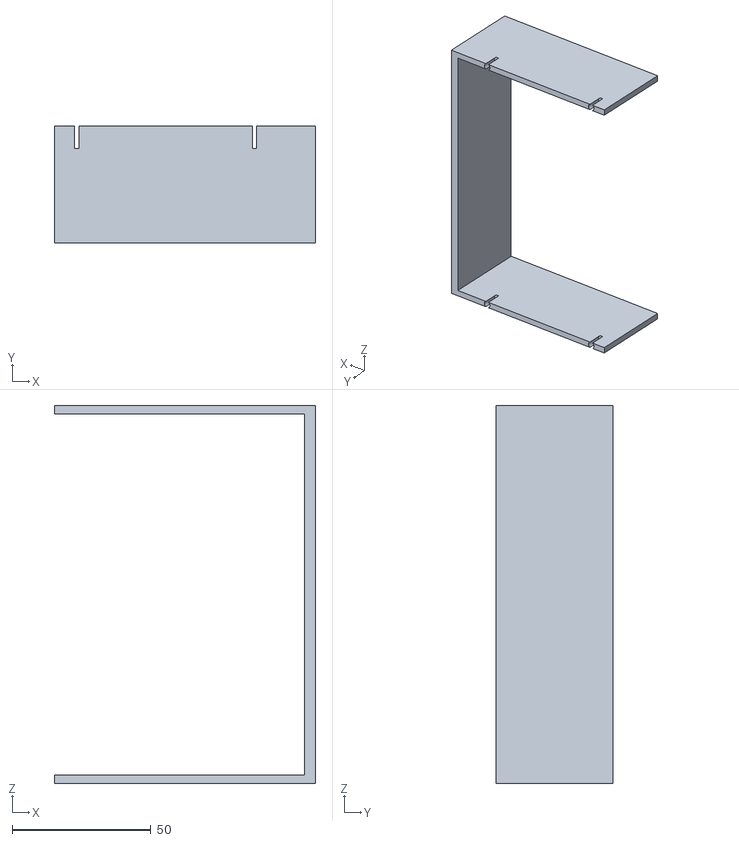
[picture p123: CAD file, 2026-09-18]
hardware/enclosure/stl/v0.4.0/lm1_sun_hood_v0.4.0.stl
94.0 x 42.0 x 136.0
