Tenejakin/LM1/hardware/enclosure/stl/v0.7.2-vertical-development/lm1_camera_tilt_rail_18deg_v0.7.2.stl

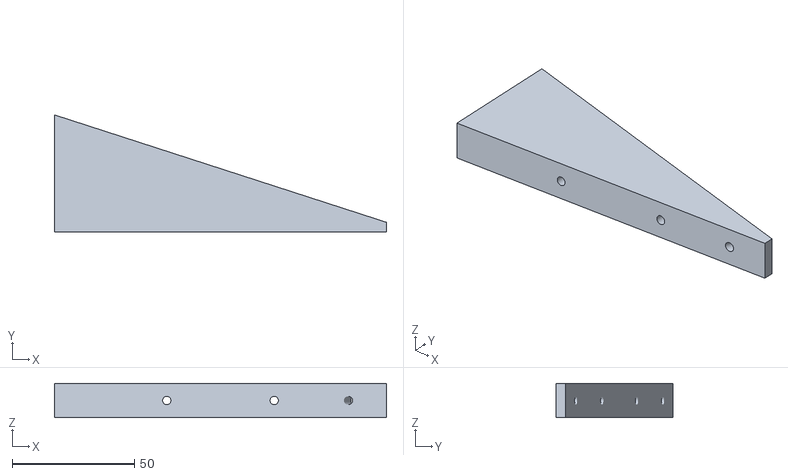
[picture p124: CAD file, 2026-10-06]
hardware/enclosure/stl/v0.7.2-vertical-development/lm1_camera_tilt_rail_18deg_v0.7.2.stl
136.0 x 48.0 x 14.0
