Tenejakin/LM1/hardware/enclosure/stl/v0.4.0/lm1_oled_swivel_base_v0.4.0.stl

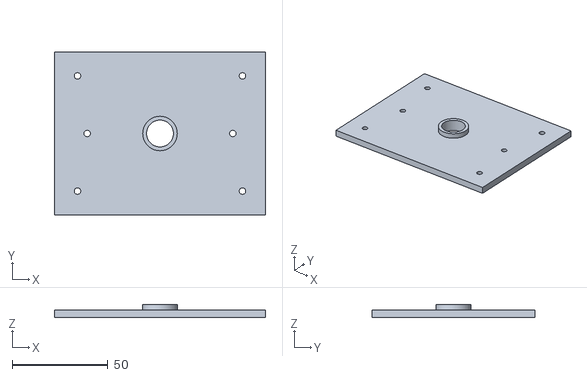
[picture p125: CAD file, 2026-09-18]
hardware/enclosure/stl/v0.4.0/lm1_oled_swivel_base_v0.4.0.stl
110.0 x 85.0 x 7.00
