Tenejakin/LM1/hardware/enclosure/stl/v0.7.2-vertical-development/lm1_camera_board_cover_v0.7.2.stl

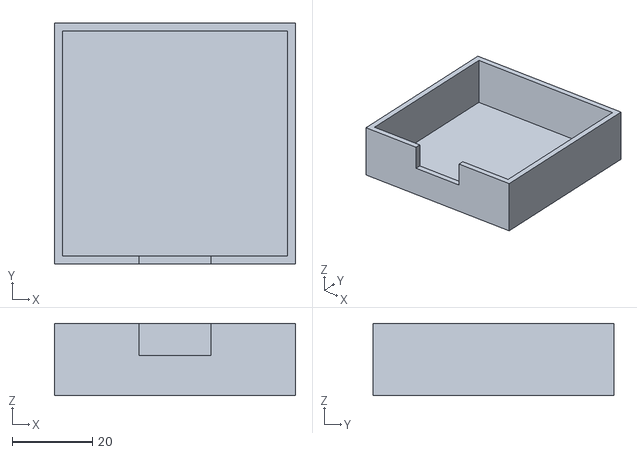
[picture p126: CAD file, 2026-10-06]
hardware/enclosure/stl/v0.7.2-vertical-development/lm1_camera_board_cover_v0.7.2.stl
60.0 x 60.0 x 18.0
