Tenejakin/LM1/hardware/enclosure/stl/v0.7.2-vertical-development/lm1_power_pack_box_v0.7.2.stl

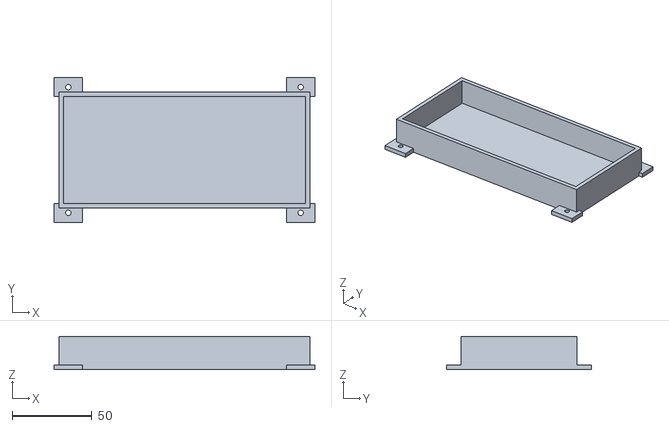
[picture p127: CAD file, 2026-10-06]
hardware/enclosure/stl/v0.7.2-vertical-development/lm1_power_pack_box_v0.7.2.stl
164.0 x 91.0 x 21.0
