Tenejakin/LM1/hardware/enclosure/stl/v0.7.2-vertical-development/lm1_vertical_mast_upper_v0.7.2.stl

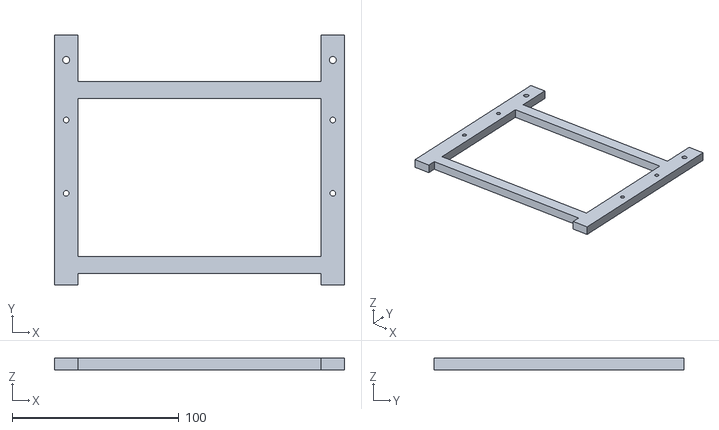
[picture p128: CAD file, 2026-10-06]
hardware/enclosure/stl/v0.7.2-vertical-development/lm1_vertical_mast_upper_v0.7.2.stl
174.0 x 150.0 x 7.00
