Tenejakin/LM1/hardware/enclosure/stl/v0.7.2-vertical-development/lm1_lipo_box_provisional_v0.7.2.stl

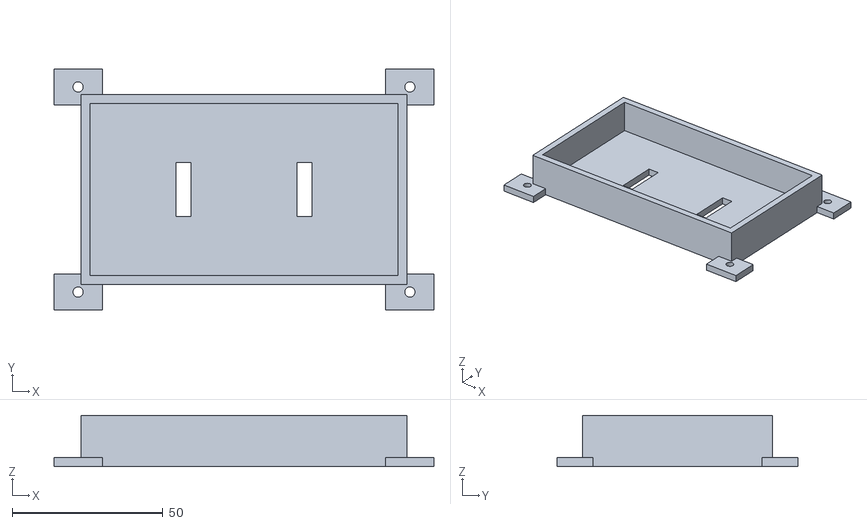
[picture p129: CAD file, 2026-10-06]
hardware/enclosure/stl/v0.7.2-vertical-development/lm1_lipo_box_provisional_v0.7.2.stl
126.0 x 80.0 x 17.0
