Tenejakin/LM1/camera-tests/diagnostics/ball-present.jpg

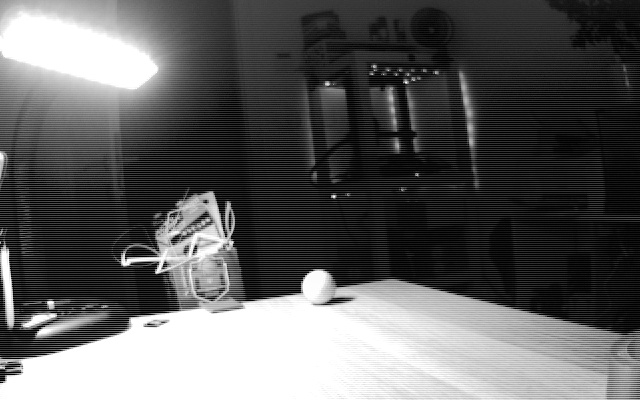
camera-tests/diagnostics/ball-present.jpg
