Tenejakin/LM1/camera-tests/diagnostics/current.jpg

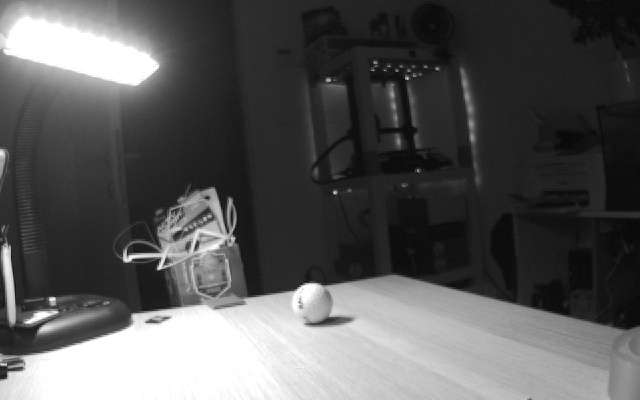
camera-tests/diagnostics/current.jpg
