Tenejakin/LM1/camera-tests/diagnostics/lm1-camera-1-v1.0.0.jpg

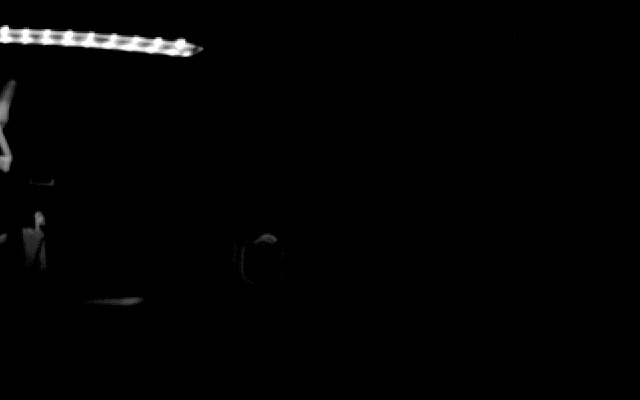
camera-tests/diagnostics/lm1-camera-1-v1.0.0.jpg
