Tenejakin/LM1/camera-tests/dual-v1.0.0/camera-latest.jpg

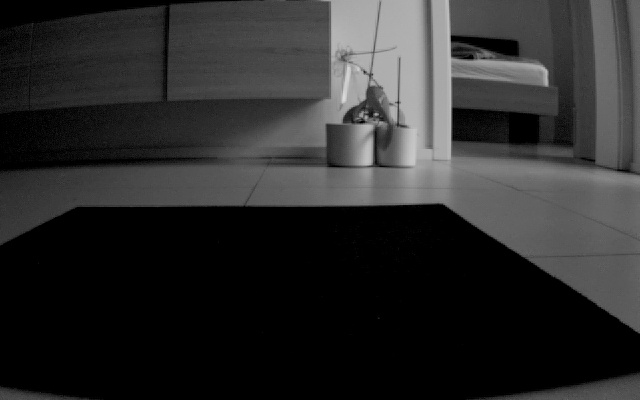
camera-tests/dual-v1.0.0/camera-latest.jpg
