Tenejakin/LM1/camera-tests/latest-live.jpg

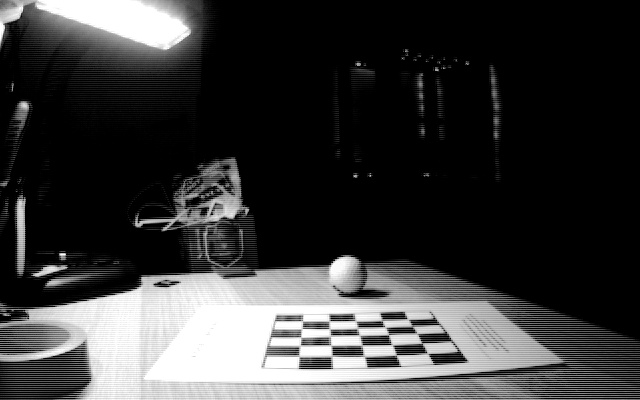
camera-tests/latest-live.jpg
