Tenejakin/LM1/hardware/enclosure/stl/v0.5.3-test/preview.png

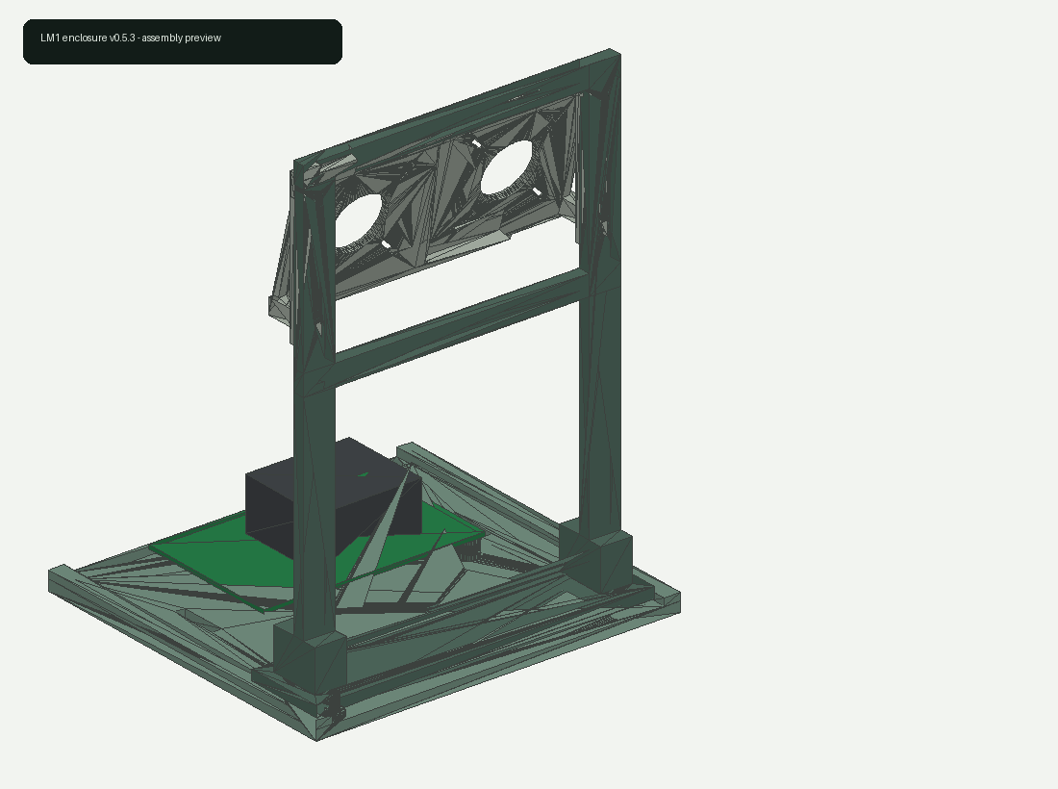
hardware/enclosure/stl/v0.5.3-test/preview.png
