Tenejakin/LM1/tmp/edge-fit-experiment-v1.0.0.jpg

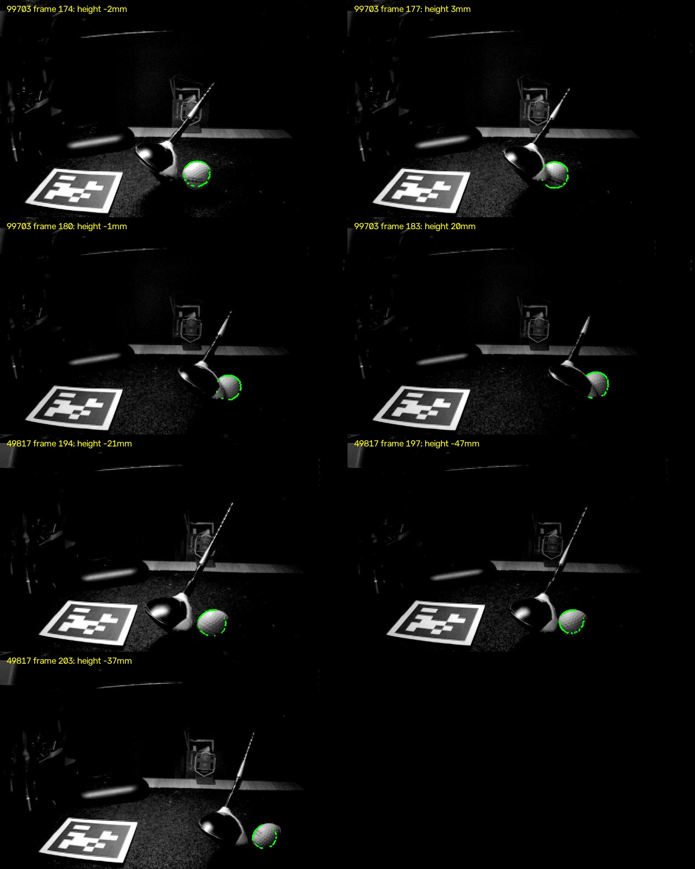
tmp/edge-fit-experiment-v1.0.0.jpg
