Tenejakin/LM1/raspberry_pi/readiness.py

"""Pre-shot readiness: find setup faults when the ball is placed, not after the swing.

Version 1.0.0. Each check reuses the gate that would fail the shot later, applied
to the still frames the detector already holds when it arms:

* ground calibration loads for the lower camera;
* the top camera sees the resting ball where the shared calibration puts it
  (the same 15 px and 5 mm limits the stereo fit applies after impact);
* the fixed exposure keeps motion blur within the 4 mm limit at this club's
  typical full-swing ball speed.

The result is advisory. A still frame can mislead the circle finder, so nothing
here blocks a capture; it only says which later gate is expected to fail and why.
"""

from __future__ import annotations

import math
import os
from datetime import datetime, timezone
from typing import Any

import numpy as np

from flight_model import CLUB_BALL_SPEED_MPS
from launch_measurements import (MAX_MOTION_BLUR_M, RADIUS, RIG_MAX_SURFACE_OFFSET_MM, load_setup,
                                 secondary_camera, stored_ground_pose)
from rig_pose import ground_mode, level_rig_pose

# Search the top view this far around the ground-plane prediction. Wider than the
# 15 px pass limit so a ball that is off can be found and the offset reported.
UPPER_SEARCH_PX = 60.0
# The level rig's camera height is a stand constant, so the ball can sit further from the prediction.
RIG_UPPER_SEARCH_PX = 100.0
MPS_TO_MPH = 2.23694


def _item(check_id: str, label: str, status: str, detail: str, **values: Any) -> dict[str, Any]:
    return {"id": check_id, "label": label, "status": status, "detail": detail, **values}


def _lower_rest_pixel(camera: dict[str, Any], image: Any, bounds: tuple[int, int, int, int]) -> np.ndarray:
    """Sub-pixel resting centre: the detector box refined by a ball-sized circle fit."""
    from stereo_check import _circle_candidates, _gray
    x, y, width, height = bounds
    approximate = np.array([x + width / 2, y + height / 2], float)
    radius = max(width, height) / 2
    nearby = [circle for circle in _circle_candidates(_gray(image), radius)
              if np.linalg.norm(circle[:2] - approximate) <= max(12.0, radius * 2.0)]
    if not nearby:
        return approximate
    return min(nearby, key=lambda circle: np.linalg.norm(circle[:2] - approximate))[:2].astype(float)


def stereo_rest_check(lower: dict[str, Any], upper: dict[str, Any], lower_image: Any, upper_image: Any,
                      bounds: tuple[int, int, int, int], level_rig: bool = False) -> dict[str, Any]:
    """Locate the resting ball in both views and say whether the shared calibration still holds.

    With the level rig the ground height is a stand constant that each shot corrects from
    the ball, so the height limit is the correction limit rather than the tag-era gate.
    """
    from stereo_check import (MAX_RAY_GAP_MM, MAX_REST_HEIGHT_ERROR_MM,
                              _circle_candidates, _gray, _project, _ray, _triangulate)
    label = "Camera alignment"
    rest_px = _lower_rest_pixel(lower, lower_image, bounds)
    origin, direction = _ray(lower, rest_px)
    if abs(direction[2]) < 1e-9:
        return _item("stereo-rest", label, "fail", "The lower camera's view of the ball never meets the ground plane.")
    assumed = origin + direction * (RADIUS - origin[2]) / direction[2]
    predicted = _project(upper, [assumed])[0]
    depth = float((upper["R"] @ assumed + upper["t"])[2])
    if depth <= 0:
        return _item("stereo-rest", label, "fail", "The ball is behind the top camera according to calibration; recalibrate both cameras.")
    radius = RADIUS * upper["K"][0, 0] / depth
    lower_ray = _ray(lower, rest_px)
    candidates = []
    search_px = RIG_UPPER_SEARCH_PX if level_rig else UPPER_SEARCH_PX
    for circle in _circle_candidates(_gray(upper_image), radius):
        if np.linalg.norm(circle[:2] - predicted) > search_px:
            continue
        point, gap = _triangulate(lower_ray, _ray(upper, circle[:2]))
        candidates.append((gap, circle[:2].astype(float), point))
    if not candidates:
        return _item("stereo-rest", label, "warn",
                     f"The top camera could not find the resting ball within {search_px:.0f} px of where "
                     "calibration expects it. It may be hidden, badly lit, or a camera has moved.")
    # The true ball is the circle whose ray meets the lower camera's ray.
    gap, upper_px, point = min(candidates, key=lambda item: item[0])
    offset_px = float(np.linalg.norm(upper_px - predicted))
    gap_mm = gap * 1000
    height_error_mm = (float(point[2]) - RADIUS) * 1000
    values = {"offsetPx": round(offset_px, 1), "rayGapMm": round(gap_mm, 2),
              "heightErrorMm": round(height_error_mm, 1)}
    if gap_mm > MAX_RAY_GAP_MM:
        return _item("stereo-rest", label, "fail",
                     f"The two cameras no longer agree on where the ball is (their views miss by {gap_mm:.0f} mm, "
                     f"limit {MAX_RAY_GAP_MM:.0f} mm). A camera or the stand has moved: "
                     + ("recalibrate the camera pair." if level_rig else "recalibrate both cameras with the AprilTag."),
                     **values)
    where = "above" if height_error_mm > 0 else "below"
    if level_rig and abs(height_error_mm) > RIG_MAX_SURFACE_OFFSET_MM:
        return _item("stereo-rest", label, "fail",
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
